jhyland87/Cryocooler-Controller/hardware/kicad/cryocooler.kicad_sch

## KiCad design hardware/kicad/cryocooler.kicad_sch (2026-10-04)

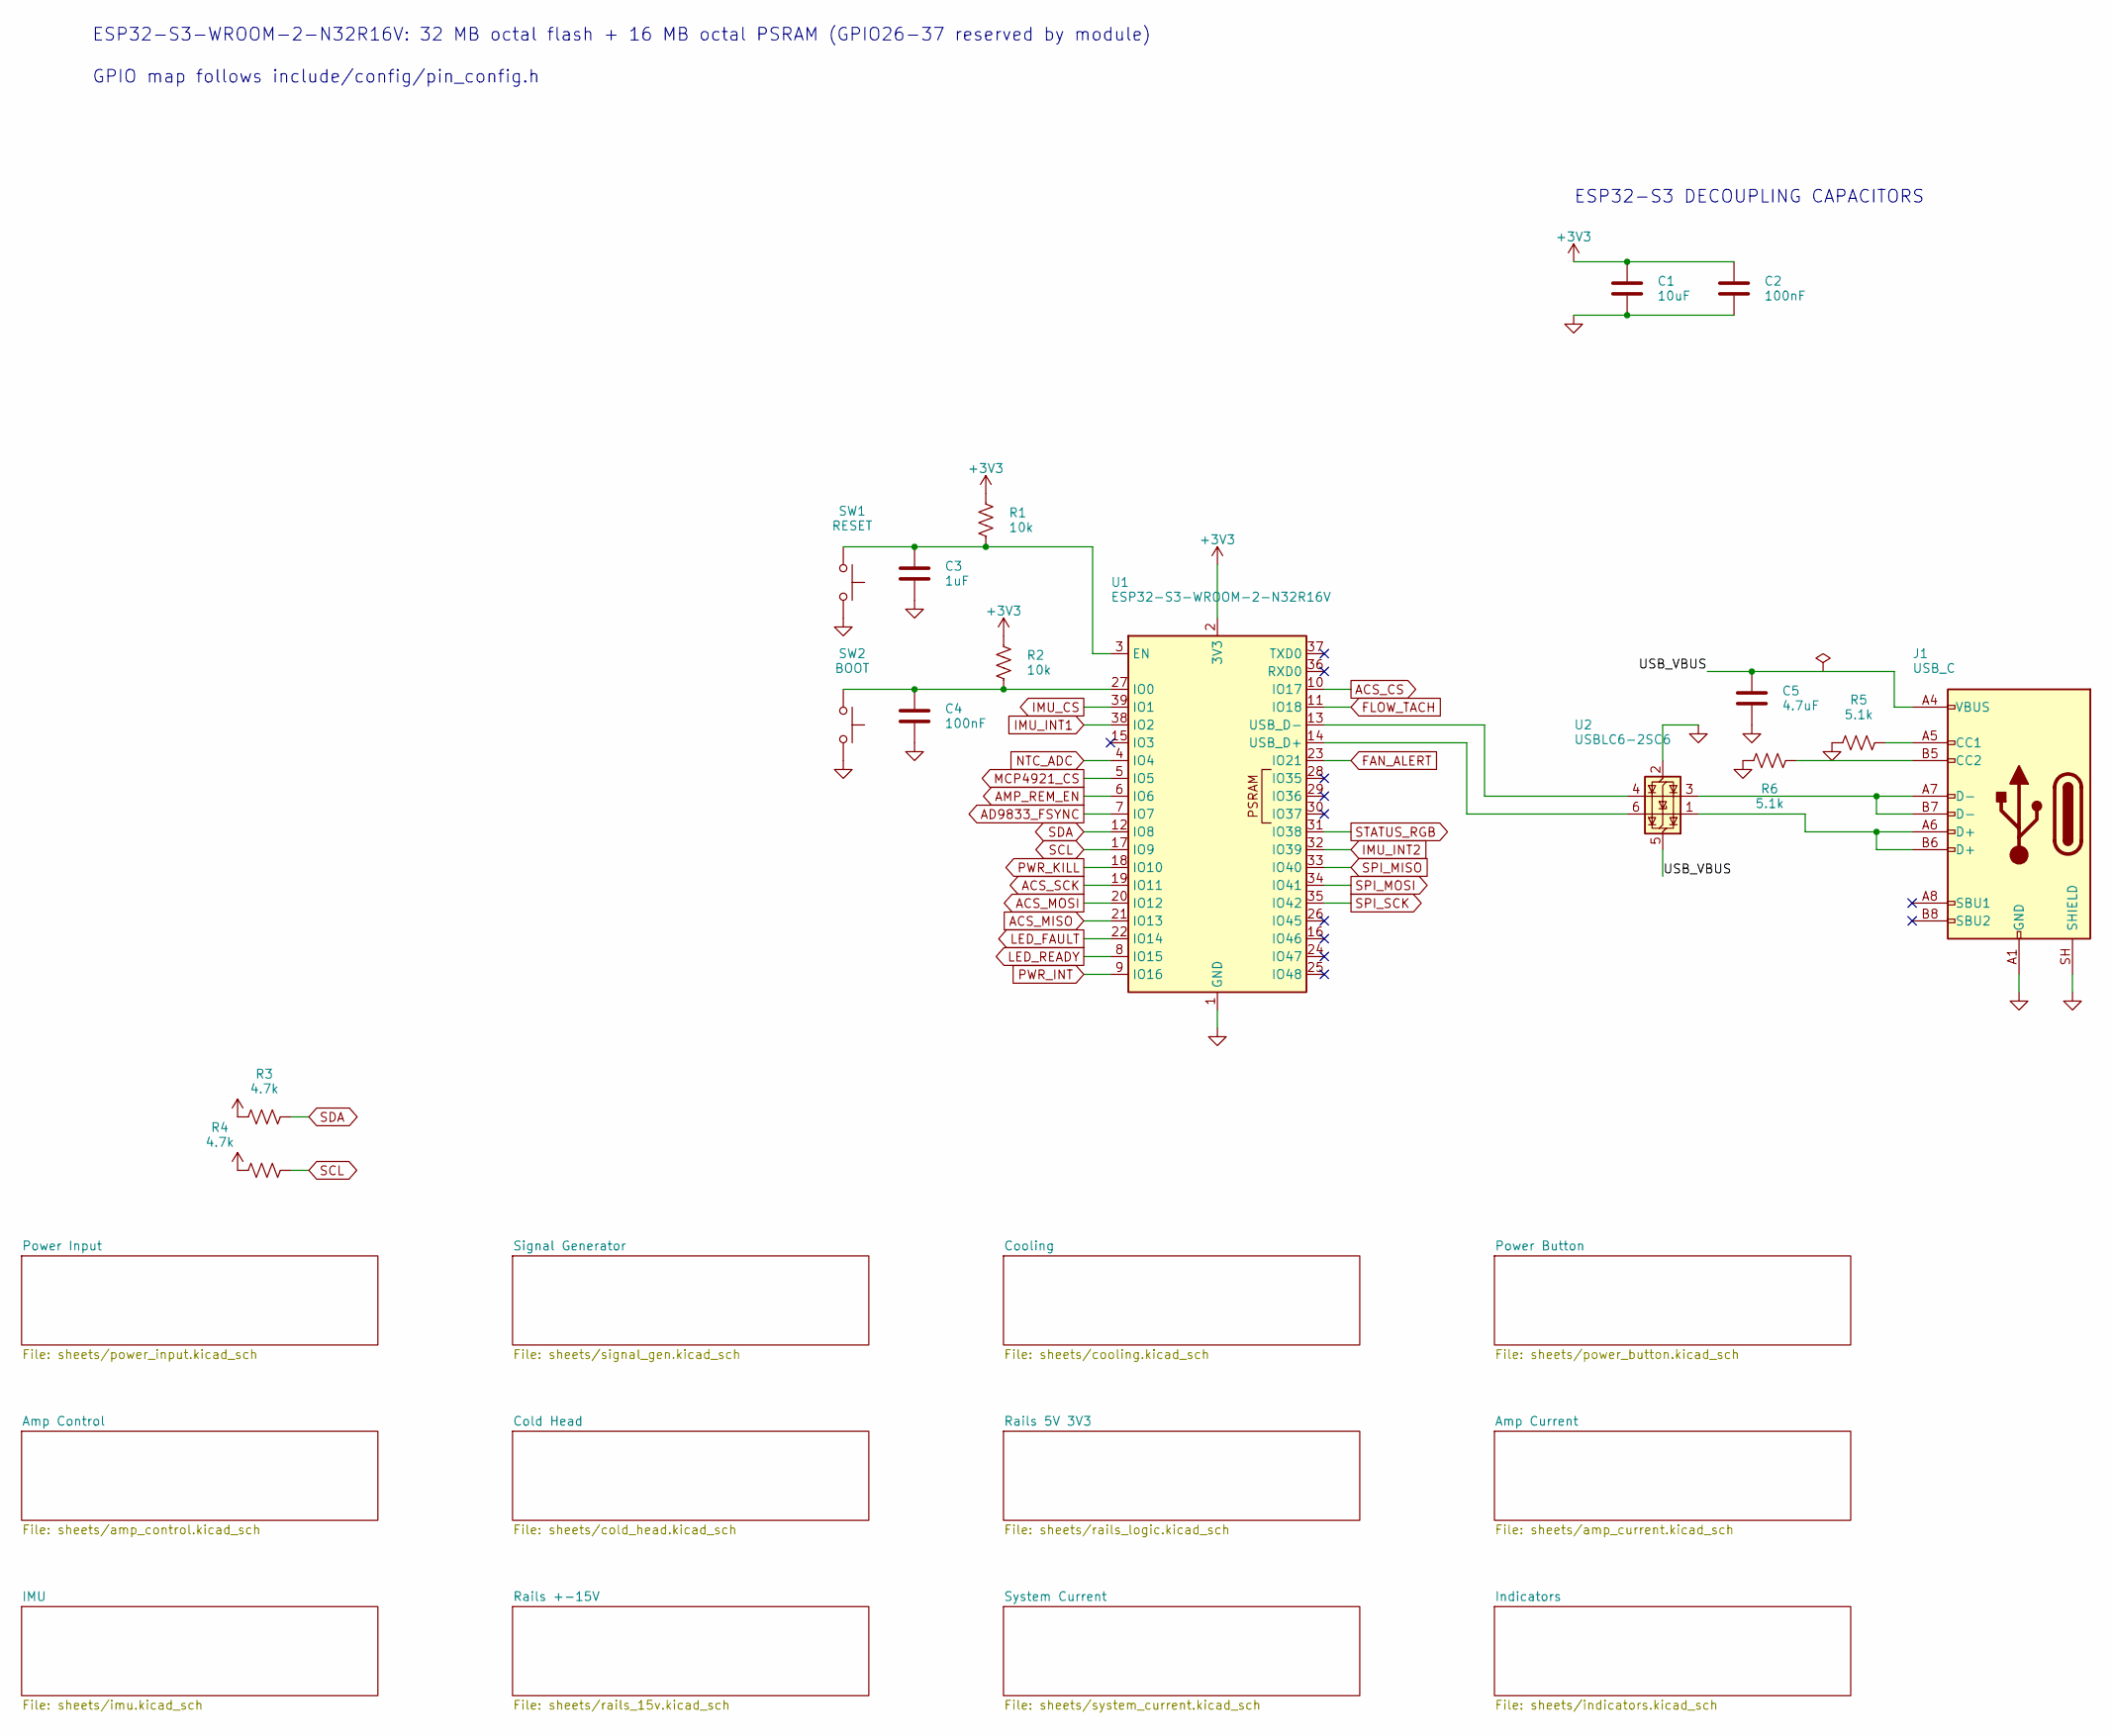
[picture p22: schematic cryocooler.kicad_sch]

Parts:
C1: 10uF; C_0805_2012Metric
C2, C4: 100nF; C_0603_1608Metric
C3: 1uF; C_0805_2012Metric
C5: 4.7uF; C_0805_2012Metric
J1: USB_C; USB_C_Receptacle_GCT_USB4105-xx-A_16P_TopMnt_Horizontal
R1, R2: 10k; R_0603_1608Metric
R3, R4: 4.7k; R_0603_1608Metric
R5, R6: 5.1k; R_0603_1608Metric
SW1: RESET; SW_SPST_TL3342
SW2: BOOT; SW_SPST_TL3342
U1: ESP32-S3-WROOM-2-N32R16V; ESP32-S3-WROOM-2
U2: USBLC6-2SC6; SOT-23-6

Connections:
+3V3: C1.1, C2.1, R1.1, R2.1, R3.1, R4.1, U1.2 (3V3)
ACS_CS: U1.10 (IO17)
ACS_MISO: U1.21 (IO13)
ACS_MOSI: U1.20 (IO12)
ACS_SCK: U1.19 (IO11)
AD9833_FSYNC: U1.7 (IO7)
AMP_REM_EN: U1.6 (IO6)
FAN_ALERT: U1.23 (IO21)
FLOW_TACH: U1.11 (IO18)
GND: C1.2, C2.2, C3.2, C4.2, C5.2, J1.A1 (GND), J1.A12 (GND), J1.B1 (GND), J1.B12 (GND), J1.SH (SHIELD), R5.1, R6.1, SW1.2, SW2.2, U1.1 (GND), U1.40 (GND), U1.41 (GND), U2.2 (GND)
IMU_CS: U1.39 (IO1)
IMU_INT1: U1.38 (IO2)
IMU_INT2: U1.32 (IO39)
LED_FAULT: U1.22 (IO14)
LED_READY: U1.8 (IO15)
MCP4921_CS: U1.5 (IO5)
NTC_ADC: U1.4 (IO4)
unnamed: C3.1, R1.2, SW1.1, U1.3 (EN)
unnamed: C4.1, R2.2, SW2.1, U1.27 (IO0)
unnamed: J1.A5 (CC1), R5.2
unnamed: J1.A6 (D+), J1.B6 (D+), U2.1 (I/O1)
unnamed: J1.A7 (D-), J1.B7 (D-), U2.3 (I/O2)
unnamed: J1.B5 (CC2), R6.2
unnamed: U1.13 (USB_D-), U2.4 (I/O2)
unnamed: U1.14 (USB_D+), U2.6 (I/O1)
PWR_INT: U1.9 (IO16)
PWR_KILL: U1.18 (IO10)
SCL: R4.2, U1.17 (IO9)
SDA: R3.2, U1.12 (IO8)
SPI_MISO: U1.33 (IO40)
SPI_MOSI: U1.34 (IO41)
SPI_SCK: U1.35 (IO42)
STATUS_RGB: U1.31 (IO38)
USB_VBUS: C5.1, J1.A4 (VBUS), J1.A9 (VBUS), J1.B4 (VBUS), J1.B9 (VBUS), U2.5 (VBUS)

Notes on the sheet:
GPIO map follows include/config/pin_config.h
ESP32-S3-WROOM-2-N32R16V: 32 MB octal flash + 16 MB octal PSRAM (GPIO26-37 reserved by module)
ESP32-S3 DECOUPLING CAPACITORS
