jhyland87/Cryocooler-Controller/hardware/kicad/sheets/amp_control.kicad_sch

## KiCad design hardware/kicad/sheets/amp_control.kicad_sch (2026-10-04)

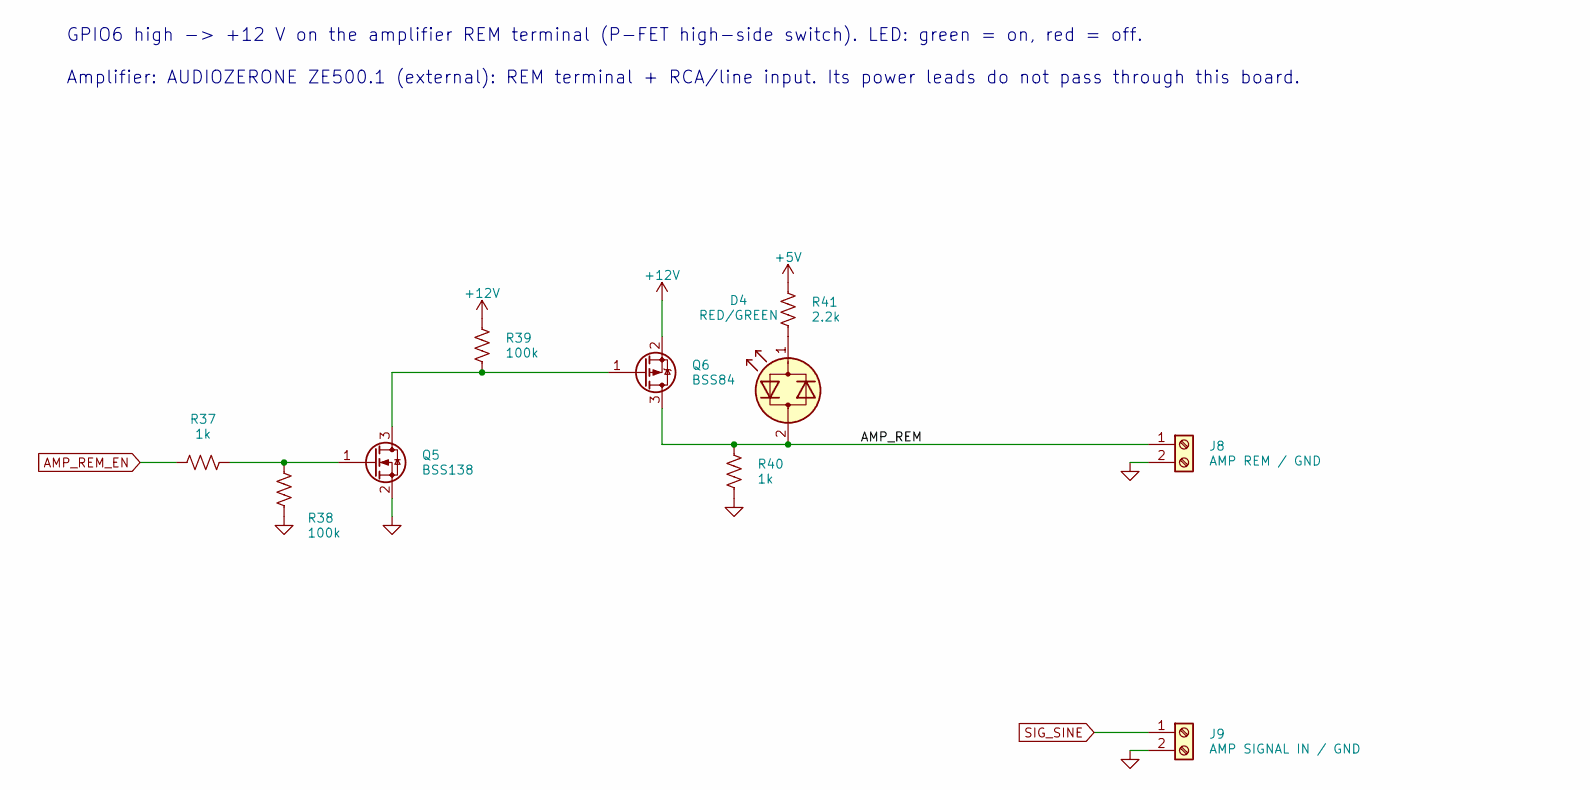
[picture p23: schematic amp_control.kicad_sch]

Parts:
D4: RED/GREEN; LED_1206_3216Metric
J8: AMP REM / GND; TerminalBlock_Phoenix_MKDS-1,5-2-5.08_1x02_P5.08mm_Horizont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
J9: AMP SIGNAL IN / GND; TerminalBlock_Phoenix_MKDS-1,5-2-5.08_1x02_P5.08mm_Horizont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
Q5: BSS138; SOT-23
Q6: BSS84; SOT-23
R37, R40: 1k; R_0603_1608Metric
R38, R39: 100k; R_0603_1608Metric
R41: 2.2k; R_0603_1608Metric

Connections:
+5V: R41.1
+12V: Q6.2 (S), R39.1
AMP_REM: D4.2 (AK), J8.1, Q6.3 (D), R40.1
AMP_REM_EN: R37.1
GND: J8.2, J9.2, Q5.2 (S), R38.2, R40.2
unnamed: D4.1 (KA), R41.2
unnamed: Q5.1 (G), R37.2, R38.1
unnamed: Q5.3 (D), Q6.1 (G), R39.2
SIG_SINE: J9.1

Notes on the sheet:
Amplifier: AUDIOZERONE ZE500.1 (external): REM terminal + RCA/line input. Its power leads do not pass through this board.
GPIO6 high -> +12 V on the amplifier REM terminal (P-FET high-side switch). LED: green = on, red = off.
