jhyland87/Cryocooler-Controller/hardware/kicad/sheets/amp_current.kicad_sch

## KiCad design hardware/kicad/sheets/amp_current.kicad_sch (2026-10-04)

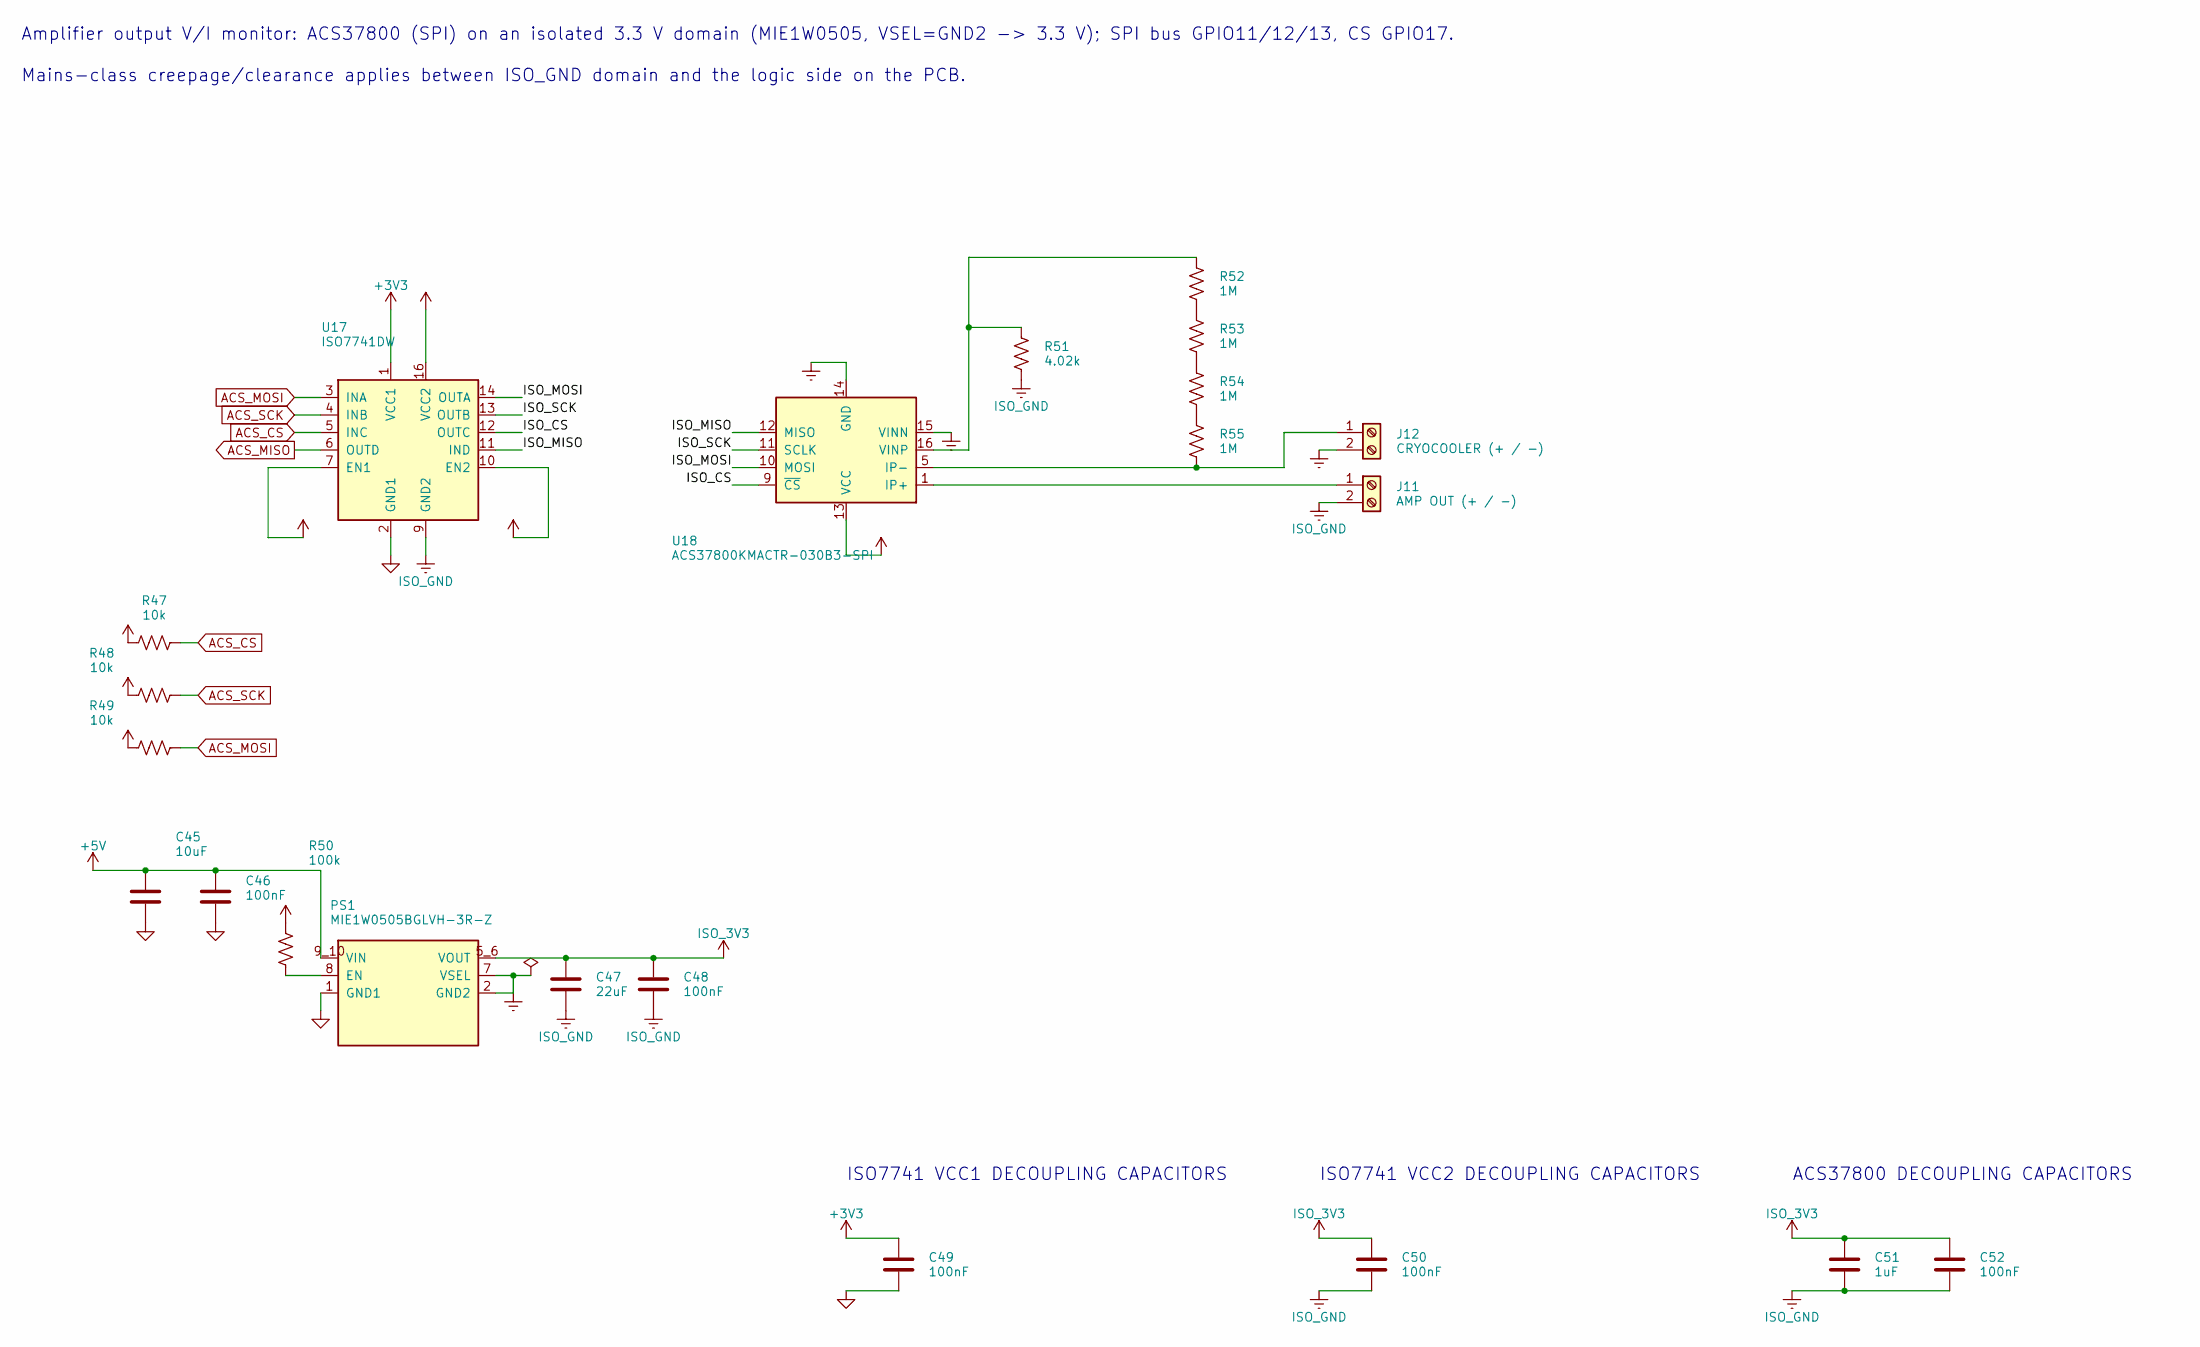
[picture p24: schematic amp_current.kicad_sch]

Parts:
C45: 10uF; C_0805_2012Metric
C46, C48, C49, C50, C52: 100nF; C_0603_1608Metric
C47: 22uF; C_1206_3216Metric
C51: 1uF; C_0805_2012Metric
J11: AMP OUT (+ / -); TerminalBlock_Phoenix_MKDS-1,5-2-5.08_1x02_P5.08mm_Horizont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
J12: CRYOCOOLER (+ / -); TerminalBlock_Phoenix_MKDS-1,5-2-5.08_1x02_P5.08mm_Horizont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
PS1: MIE1W0505BGLVH-3R-Z; CONV_MIE1W0505BGLVH-3R-Z
R47, R48, R49: 10k; R_0603_1608Metric
R50: 100k; R_0603_1608Metric
R51: 4.02k; R_0603_1608Metric
R52, R53, R54, R55: 1M; R_1206_3216Metric
U17: ISO7741DW; SOIC-16W_7.5x10.3mm_P1.27mm
U18: ACS37800KMACTR-030B3-SPI; SOIC-16W_7.5x10.3mm_P1.27mm

Connections:
+3V3: C49.1, R47.1, R48.1, R49.1, U17.1 (VCC1), U17.7 (EN1)
+5V: C45.1, C46.1, PS1.9_10 (VIN), R50.1
ACS_CS: R47.2, U17.5 (INC)
ACS_MISO: U17.6 (OUTD)
ACS_MOSI: R49.2, U17.3 (INA)
ACS_SCK: R48.2, U17.4 (INB)
GND: C45.2, C46.2, C49.2, PS1.1 (GND1), PS1.11_12 (GND1), U17.2 (GND1), U17.8 (GND1)
ISO_3V3: C47.1, C48.1, C50.1, C51.1, C52.1, PS1.5_6 (VOUT), U17.10 (EN2), U17.16 (VCC2), U18.13 (VCC)
ISO_CS: U17.12 (OUTC), U18.9 (~CS)
ISO_GND: C47.2, C48.2, C50.2, C51.2, C52.2, J11.2, J12.2, PS1.2 (GND2), PS1.3_4 (GND2), PS1.7 (VSEL), R51.2, U17.9 (GND2), U17.15 (GND2), U18.14 (GND), U18.15 (VINN)
ISO_MISO: U17.11 (IND), U18.12 (MISO)
ISO_MOSI: U17.14 (OUTA), U18.10 (MOSI)
ISO_SCK: U17.13 (OUTB), U18.11 (SCLK)
unnamed: J11.1, U18.1 (IP+), U18.2 (IP+), U18.3 (IP+), U18.4 (IP+)
unnamed: J12.1, R55.2, U18.5 (IP-), U18.6 (IP-), U18.7 (IP-), U18.8 (IP-)
unnamed: PS1.8 (EN), R50.2
unnamed: R51.1, R52.1, U18.16 (VINP)
unnamed: R52.2, R53.1
unnamed: R53.2, R54.1
unnamed: R54.2, R55.1

Notes on the sheet:
ACS37800 DECOUPLING CAPACITORS
ISO7741 VCC1 DECOUPLING CAPACITORS
Amplifier output V/I monitor: ACS37800 (SPI) on an isolated 3.3 V domain (MIE1W0505, VSEL=GND2 -> 3.3 V); SPI bus GPIO11/12/13, CS GPIO17.
ISO7741 VCC2 DECOUPLING CAPACITORS
Mains-class creepage/clearance applies between ISO_GND domain and the logic side on the PCB.
