jhyland87/Cryocooler-Controller/hardware/kicad/sheets/cold_head.kicad_sch

## KiCad design hardware/kicad/sheets/cold_head.kicad_sch (2026-10-04)

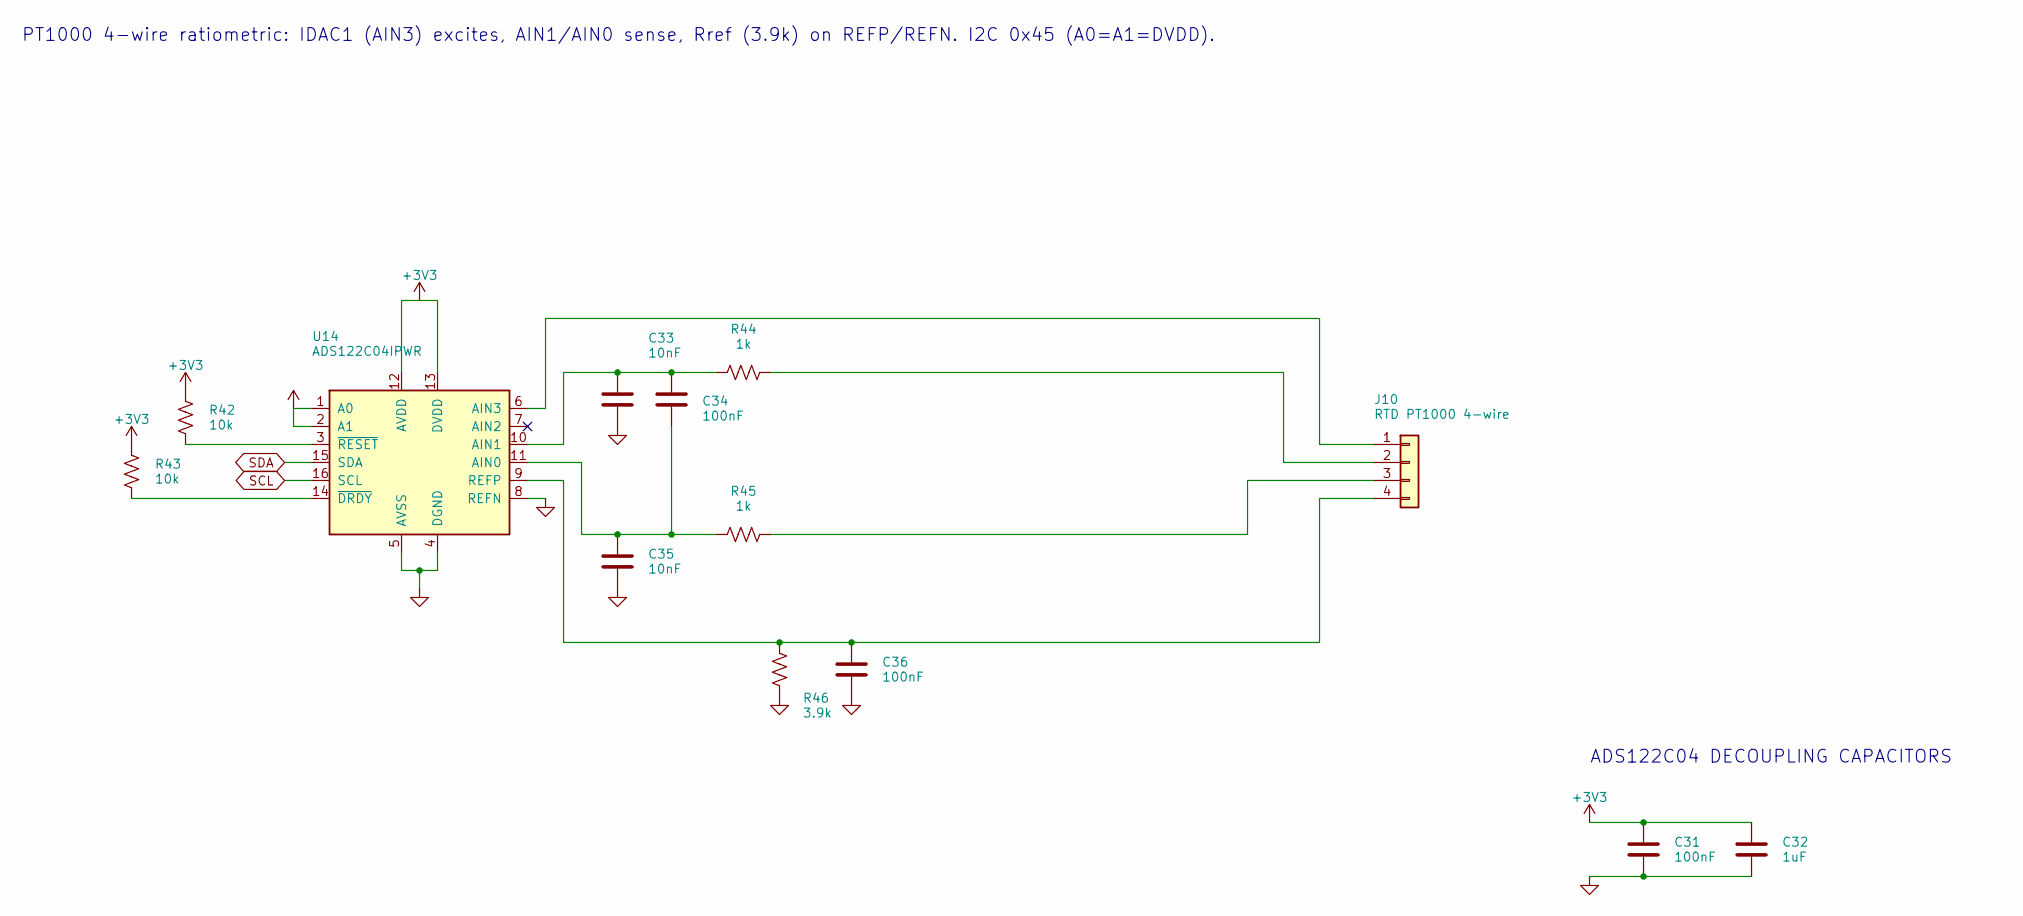
[picture p25: schematic cold_head.kicad_sch]

Parts:
C31, C34, C36: 100nF; C_0603_1608Metric
C32: 1uF; C_0805_2012Metric
C33, C35: 10nF; C_0603_1608Metric
J10: RTD PT1000 4-wire; JST_XH_B4B-XH-A_1x04_P2.50mm_Vertical
R42, R43: 10k; R_0603_1608Metric
R44, R45: 1k; R_0603_1608Metric
R46: 3.9k; R_0603_1608Metric
U14: ADS122C04IPWR; TSSOP-16_4.4x5mm_P0.65mm

Connections:
+3V3: C31.1, C32.1, R42.1, R43.1, U14.1 (A0), U14.2 (A1), U14.12 (AVDD), U14.13 (DVDD)
GND: C31.2, C32.2, C33.2, C35.2, C36.2, R46.2, U14.4 (DGND), U14.5 (AVSS), U14.8 (REFN)
unnamed: C33.1, C34.1, R44.1, U14.10 (AIN1)
unnamed: C34.2, C35.1, R45.1, U14.11 (AIN0)
unnamed: C36.1, J10.4, R46.1, U14.9 (REFP)
unnamed: J10.1, U14.6 (AIN3)
unnamed: J10.2, R44.2
unnamed: J10.3, R45.2
unnamed: R42.2, U14.3 (~RESET)
unnamed: R43.2, U14.14 (~DRDY)
SCL: U14.16 (SCL)
SDA: U14.15 (SDA)

Notes on the sheet:
ADS122C04 DECOUPLING CAPACITORS
PT1000 4-wire ratiometric: IDAC1 (AIN3) excites, AIN1/AIN0 sense, Rref (3.9k) on REFP/REFN. I2C 0x45 (A0=A1=DVDD).
