jhyland87/Cryocooler-Controller/hardware/kicad/sheets/cooling.kicad_sch

## KiCad design hardware/kicad/sheets/cooling.kicad_sch (2026-10-04)

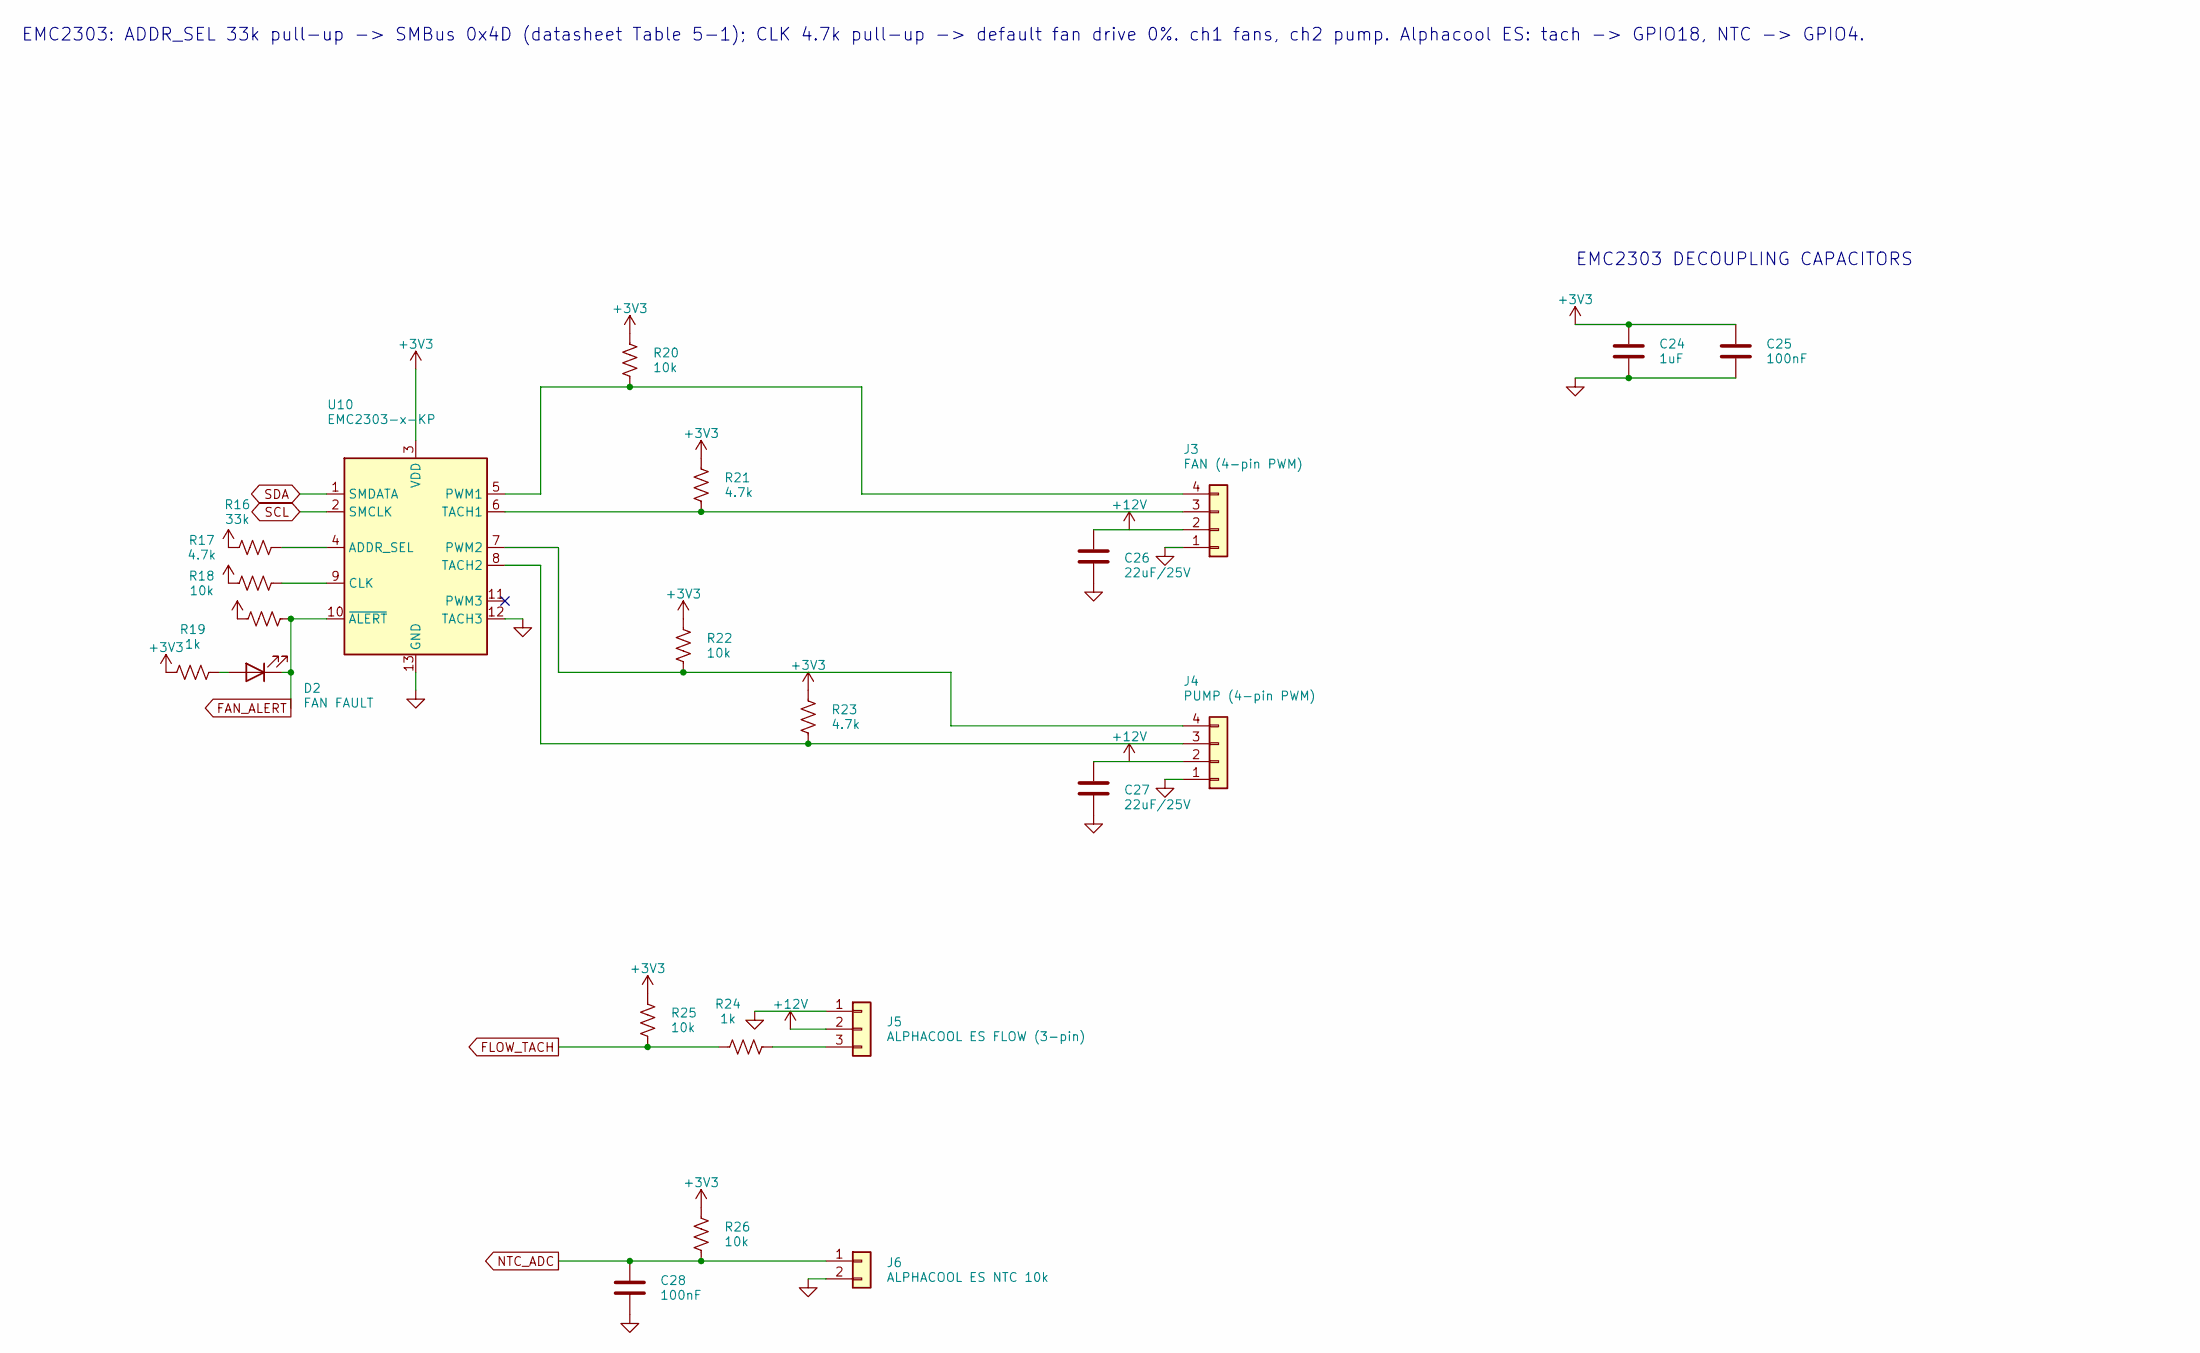
[picture p26: schematic cooling.kicad_sch]

Parts:
C24: 1uF; C_0805_2012Metric
C25, C28: 100nF; C_0603_1608Metric
C26, C27: 22uF/25V; C_1210_3225Metric
D2: FAN FAULT; LED_0603_1608Metric
J3: FAN (4-pin PWM); Molex_KK-254_AE-6410-04A_1x04_P2.54mm_Vertical
J4: PUMP (4-pin PWM); Molex_KK-254_AE-6410-04A_1x04_P2.54mm_Vertical
J5: ALPHACOOL ES FLOW (3-pin); Molex_KK-254_AE-6410-03A_1x03_P2.54mm_Vertical
J6: ALPHACOOL ES NTC 10k; JST_XH_B2B-XH-A_1x02_P2.50mm_Vertical
R16: 33k; R_0603_1608Metric
R17, R21, R23: 4.7k; R_0603_1608Metric
R18, R20, R22, R25, R26: 10k; R_0603_1608Metric
R19, R24: 1k; R_0603_1608Metric
U10: EMC2303-x-KP; VQFN-12-1EP_4x4mm_P0.8mm_EP2.1x2.1mm_ThermalVias

Connections:
+3V3: C24.1, C25.1, R16.1, R17.1, R18.1, R19.1, R20.1, R21.1, R22.1, R23.1, R25.1, R26.1, U10.3 (VDD)
+12V: C26.1, C27.1, J3.2, J4.2, J5.2
FAN_ALERT: D2.1 (K), R18.2, U10.10 (~ALERT)
FLOW_TACH: R24.1, R25.2
GND: C24.2, C25.2, C26.2, C27.2, C28.2, J3.1, J4.1, J5.1, J6.2, U10.12 (TACH3), U10.13 (GND)
NTC_ADC: C28.1, J6.1, R26.2
unnamed: D2.2 (A), R19.2
unnamed: J3.3, R21.2, U10.6 (TACH1)
unnamed: J3.4, R20.2, U10.5 (PWM1)
unnamed: J4.3, R23.2, U10.8 (TACH2)
unnamed: J4.4, R22.2, U10.7 (PWM2)
unnamed: J5.3, R24.2
unnamed: R16.2, U10.4 (ADDR_SEL)
unnamed: R17.2, U10.9 (CLK)
SCL: U10.2 (SMCLK)
SDA: U10.1 (SMDATA)

Notes on the sheet:
EMC2303: ADDR_SEL 33k pull-up -> SMBus 0x4D (datasheet Table 5-1); CLK 4.7k pull-up -> default fan drive 0%. ch1 fans, ch2 pump. Alphacool ES: tach -> GPIO18, NTC -> GPIO4.
EMC2303 DECOUPLING CAPACITORS
