jhyland87/Cryocooler-Controller/hardware/kicad/sheets/imu.kicad_sch

## KiCad design hardware/kicad/sheets/imu.kicad_sch (2026-10-04)

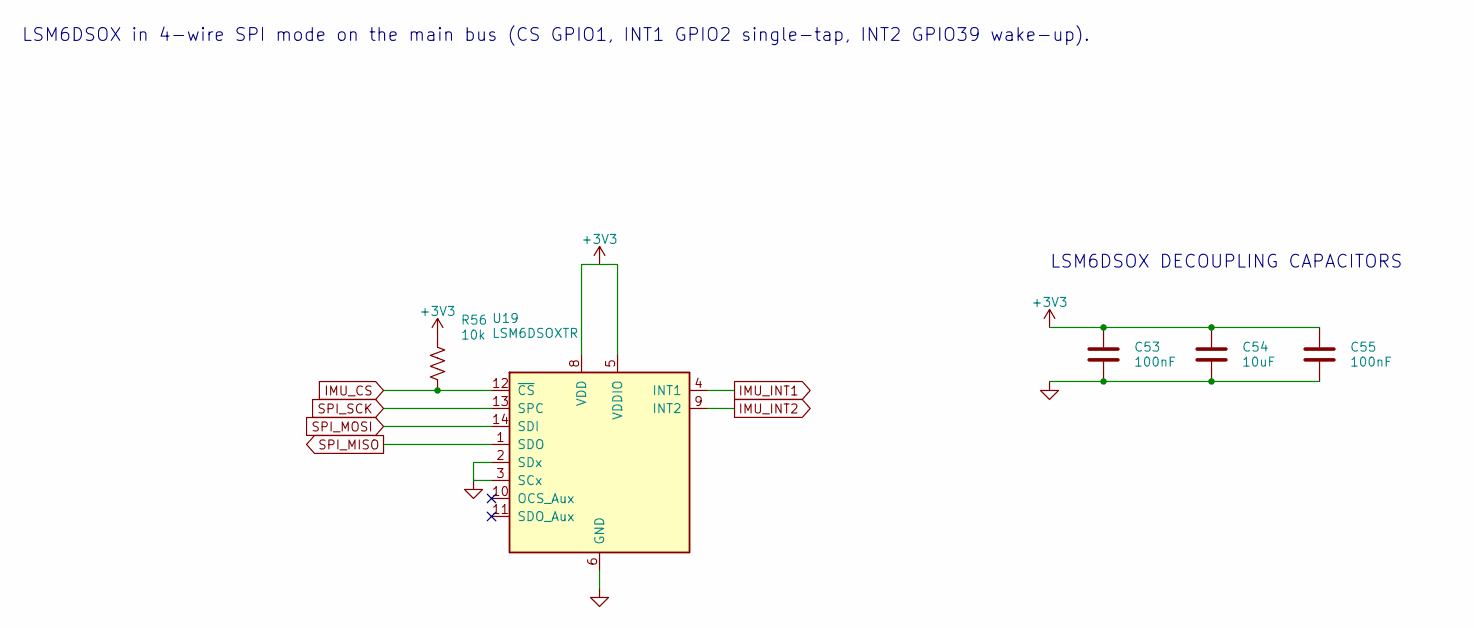
[picture p27: schematic imu.kicad_sch]

Parts:
C53, C55: 100nF; C_0603_1608Metric
C54: 10uF; C_0805_2012Metric
R56: 10k; R_0603_1608Metric
U19: LSM6DSOXTR; LGA-14_3x2.5mm_P0.5mm_LayoutBorder3x4y

Connections:
+3V3: C53.1, C54.1, C55.1, R56.1, U19.5 (VDDIO), U19.8 (VDD)
GND: C53.2, C54.2, C55.2, U19.2 (SDx), U19.3 (SCx), U19.6 (GND), U19.7 (GND)
IMU_CS: R56.2, U19.12 (~CS)
IMU_INT1: U19.4 (INT1)
IMU_INT2: U19.9 (INT2)
SPI_MISO: U19.1 (SDO)
SPI_MOSI: U19.14 (SDI)
SPI_SCK: U19.13 (SPC)

Notes on the sheet:
LSM6DSOX in 4-wire SPI mode on the main bus (CS GPIO1, INT1 GPIO2 single-tap, INT2 GPIO39 wake-up).
LSM6DSOX DECOUPLING CAPACITORS
