jhyland87/Cryocooler-Controller/hardware/kicad/sheets/indicators.kicad_sch

## KiCad design hardware/kicad/sheets/indicators.kicad_sch (2026-10-04)

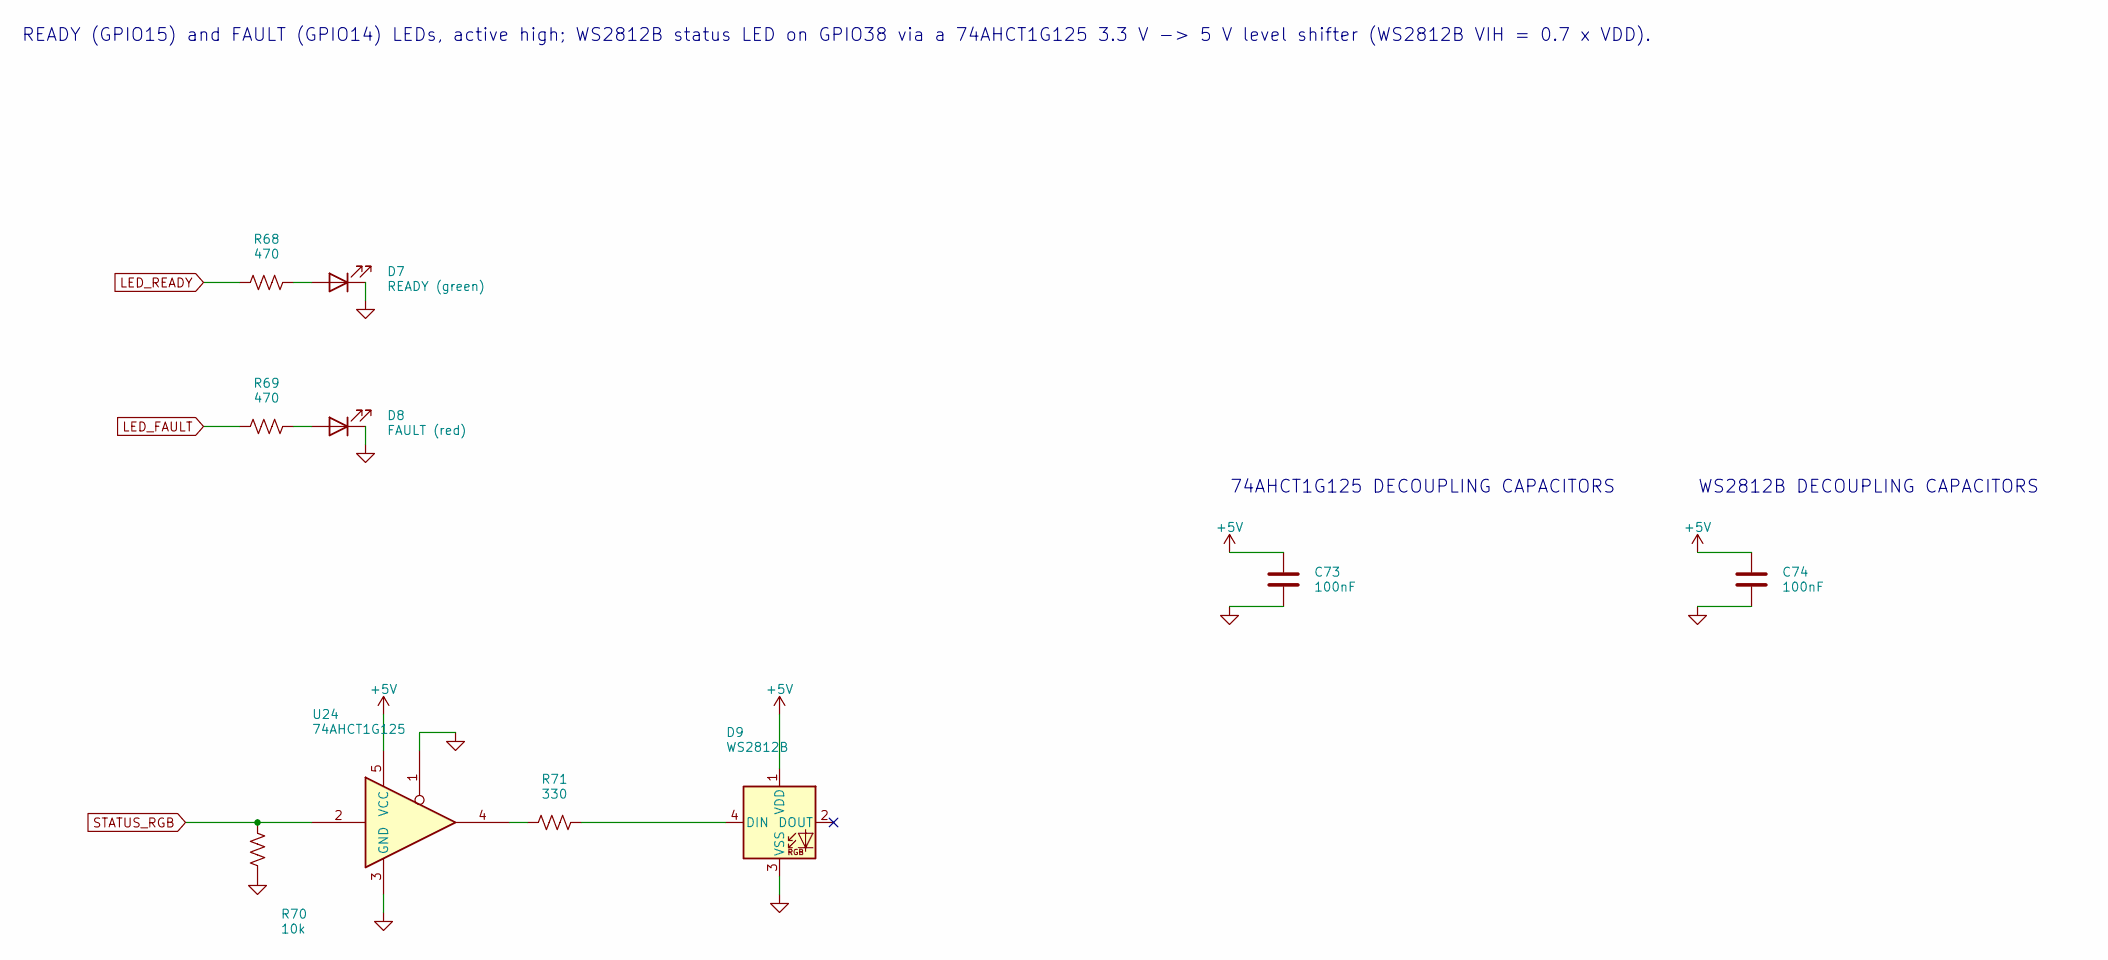
[picture p28: schematic indicators.kicad_sch]

Parts:
C73, C74: 100nF; C_0603_1608Metric
D7: READY (green); LED_0603_1608Metric
D8: FAULT (red); LED_0603_1608Metric
D9: WS2812B; LED_WS2812B_PLCC4_5.0x5.0mm_P3.2mm
R68, R69: 470; R_0603_1608Metric
R70: 10k; R_0603_1608Metric
R71: 330; R_0603_1608Metric
U24: 74AHCT1G125; SOT-23-5

Connections:
+5V: C73.1, C74.1, D9.1 (VDD), U24.5 (VCC)
GND: C73.2, C74.2, D7.1 (K), D8.1 (K), D9.3 (VSS), R70.2, U24.1, U24.3 (GND)
LED_FAULT: R69.1
LED_READY: R68.1
unnamed: D7.2 (A), R68.2
unnamed: D8.2 (A), R69.2
unnamed: D9.4 (DIN), R71.2
unnamed: R71.1, U24.4
STATUS_RGB: R70.1, U24.2

Notes on the sheet:
READY (GPIO15) and FAULT (GPIO14) LEDs, active high; WS2812B status LED on GPIO38 via a 74AHCT1G125 3.3 V -> 5 V level shifter (WS2812B VIH = 0.7 x VDD).
74AHCT1G125 DECOUPLING CAPACITORS
WS2812B DECOUPLING CAPACITORS
