jhyland87/Cryocooler-Controller/hardware/kicad/sheets/power_button.kicad_sch

## KiCad design hardware/kicad/sheets/power_button.kicad_sch (2026-10-04)

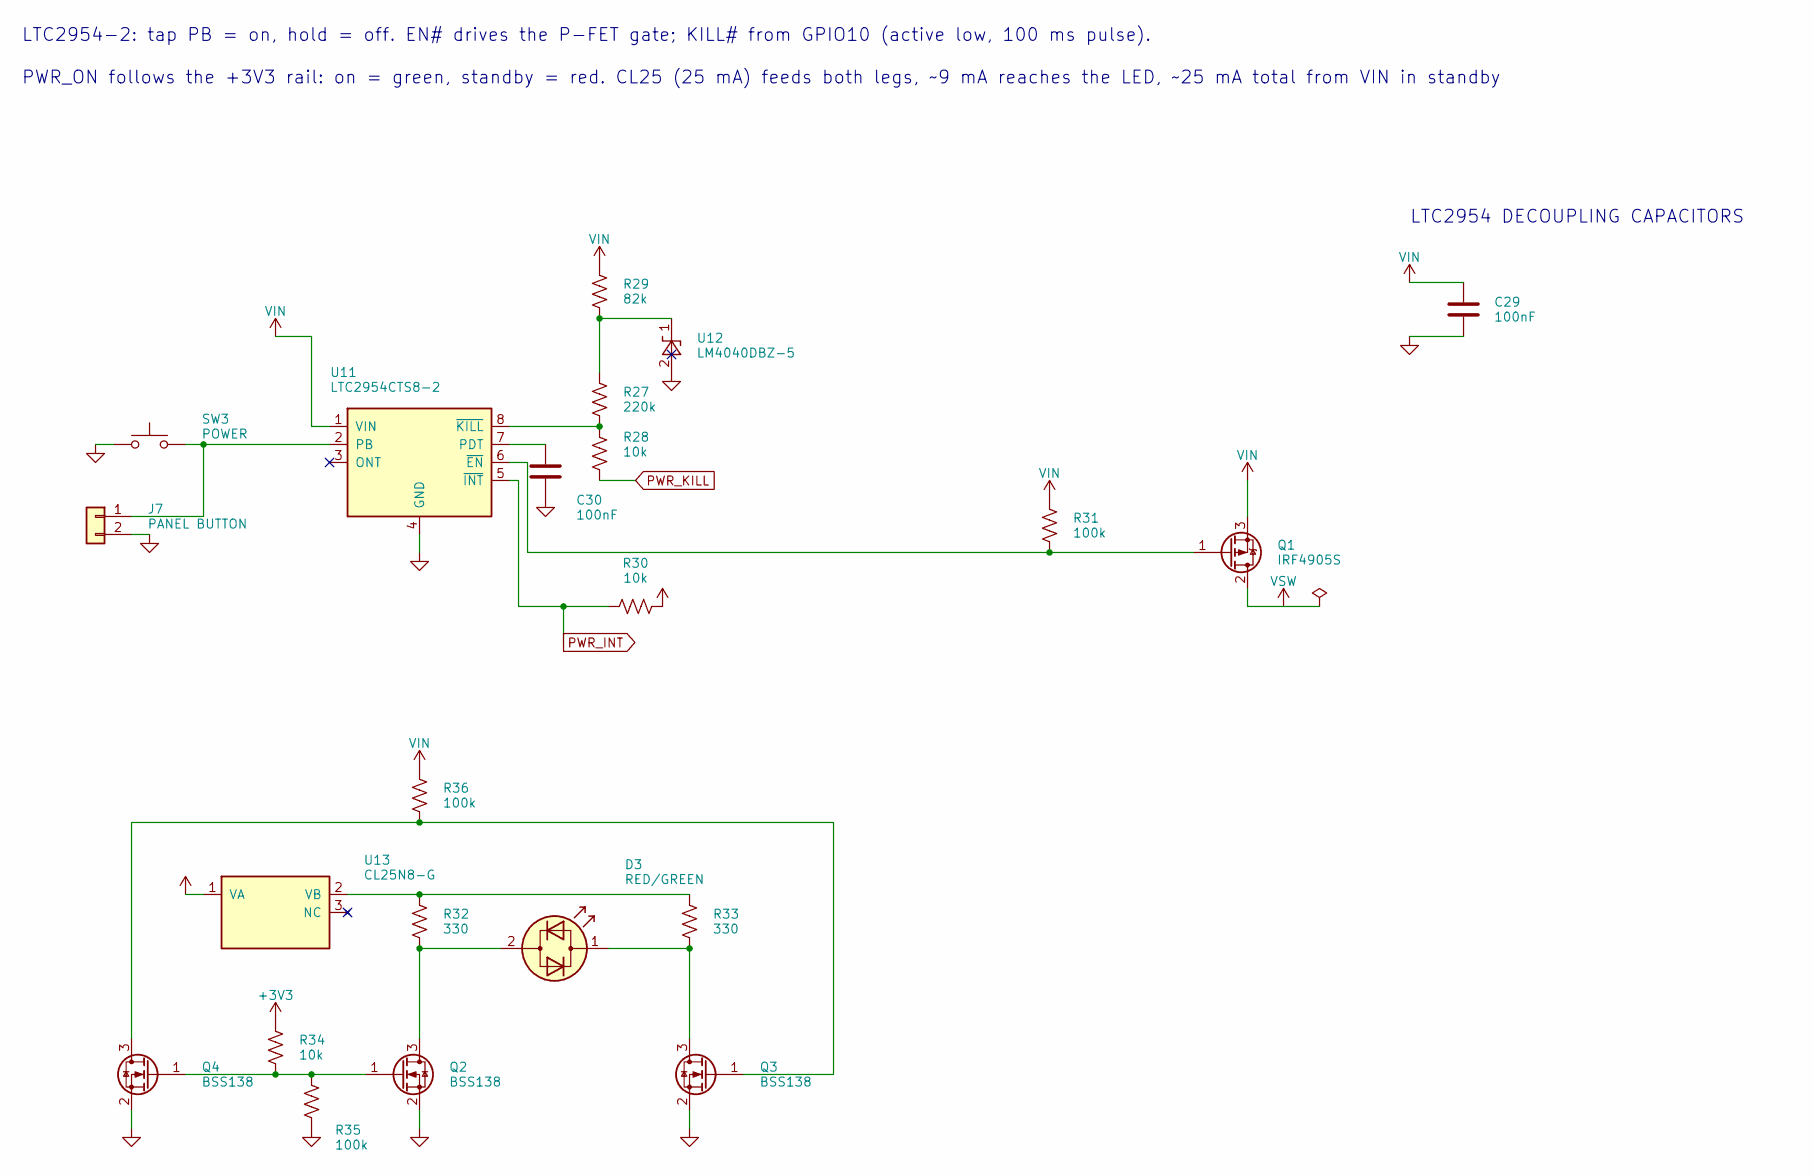
[picture p29: schematic power_button.kicad_sch]

Parts:
C29, C30: 100nF; C_0603_1608Metric
D3: RED/GREEN; LED_1206_3216Metric
J7: PANEL BUTTON; JST_XH_B2B-XH-A_1x02_P2.50mm_Vertical
Q1: IRF4905S; TO-263-3_TabPin2
Q2, Q3, Q4: BSS138; SOT-23
R27: 220k; R_0603_1608Metric
R28, R30, R34: 10k; R_0603_1608Metric
R29: 82k; R_0603_1608Metric
R31, R35, R36: 100k; R_0603_1608Metric
R32, R33: 330; R_0603_1608Metric
SW3: POWER; SW_SPST_TL3342
U11: LTC2954CTS8-2; SOT-23-8
U12: LM4040DBZ-5; SOT-23
U13: CL25N8-G; SOT-89-3

Connections:
+3V3: R30.2, R34.1
GND: C29.2, C30.2, J7.2, Q2.2 (S), Q3.2 (S), Q4.2 (S), R35.2, SW3.2, U11.4 (GND), U12.2 (A)
unnamed: C30.1, U11.7 (PDT)
unnamed: D3.1 (KA), Q3.3 (D), R33.2
unnamed: D3.2 (AK), Q2.3 (D), R32.2
unnamed: J7.1, SW3.1, U11.2 (PB)
unnamed: Q1.1 (G), R31.2, U11.6 (~EN)
unnamed: Q2.1 (G), Q4.1 (G), R34.2, R35.1
unnamed: Q3.1 (G), Q4.3 (D), R36.2
unnamed: R27.1, R29.2, U12.1 (K)
unnamed: R27.2, R28.1, U11.8 (~KILL)
unnamed: R32.1, R33.1, U13.2 (VB)
PWR_INT: R30.1, U11.5 (~INT)
PWR_KILL: R28.2
VIN: C29.1, Q1.3 (S), R29.1, R31.1, R36.1, U11.1 (VIN), U13.1 (VA)
VSW: Q1.2 (D)

Notes on the sheet:
PWR_ON follows the +3V3 rail: on = green, standby = red. CL25 (25 mA) feeds both legs, ~9 mA reaches the LED, ~25 mA total from VIN in standby
LTC2954 DECOUPLING CAPACITORS
LTC2954-2: tap PB = on, hold = off. EN# drives the P-FET gate; KILL# from GPIO10 (active low, 100 ms pulse).
