jhyland87/Cryocooler-Controller/hardware/kicad/sheets/power_input.kicad_sch

## KiCad design hardware/kicad/sheets/power_input.kicad_sch (2026-10-04)

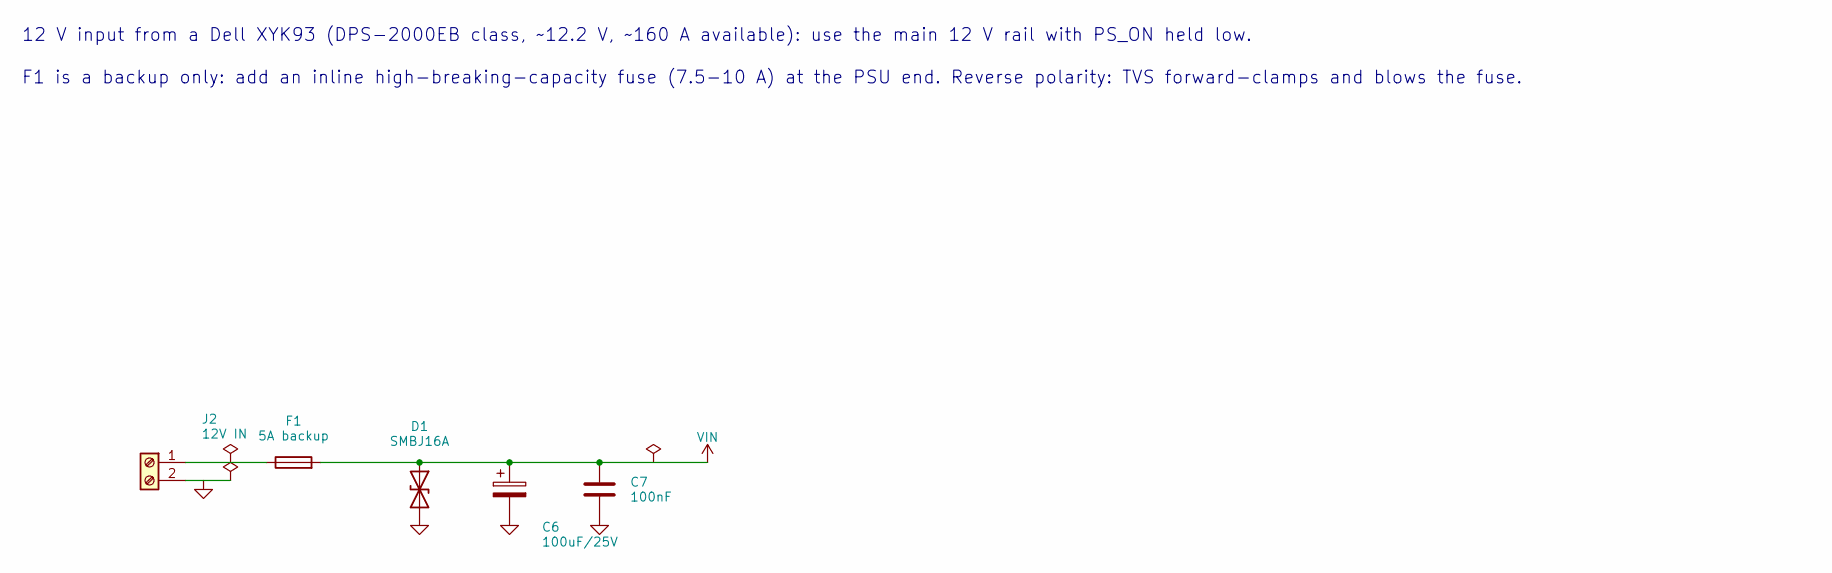
[picture p30: schematic power_input.kicad_sch]

Parts:
C6: 100uF/25V; CP_Elec_8x10
C7: 100nF; C_0805_2012Metric
D1: SMBJ16A; D_SMB
F1: 5A backup; Fuse_1812_4532Metric
J2: 12V IN; TerminalBlock_Phoenix_MKDS-1,5-2-5.08_1x02_P5.08mm_Horizont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

Connections:
GND: C6.2, C7.2, D1.2 (A2), J2.2
unnamed: F1.1, J2.1
VIN: C6.1, C7.1, D1.1 (A1), F1.2

Notes on the sheet:
12 V input from a Dell XYK93 (DPS-2000EB class, ~12.2 V, ~160 A available): use the main 12 V rail with PS_ON held low.
F1 is a backup only: add an inline high-breaking-capacity fuse (7.5-10 A) at the PSU end. Reverse polarity: TVS forward-clamps and blows the fuse.
