jhyland87/Cryocooler-Controller/hardware/kicad/sheets/rails_15v.kicad_sch

## KiCad design hardware/kicad/sheets/rails_15v.kicad_sch (2026-10-04)

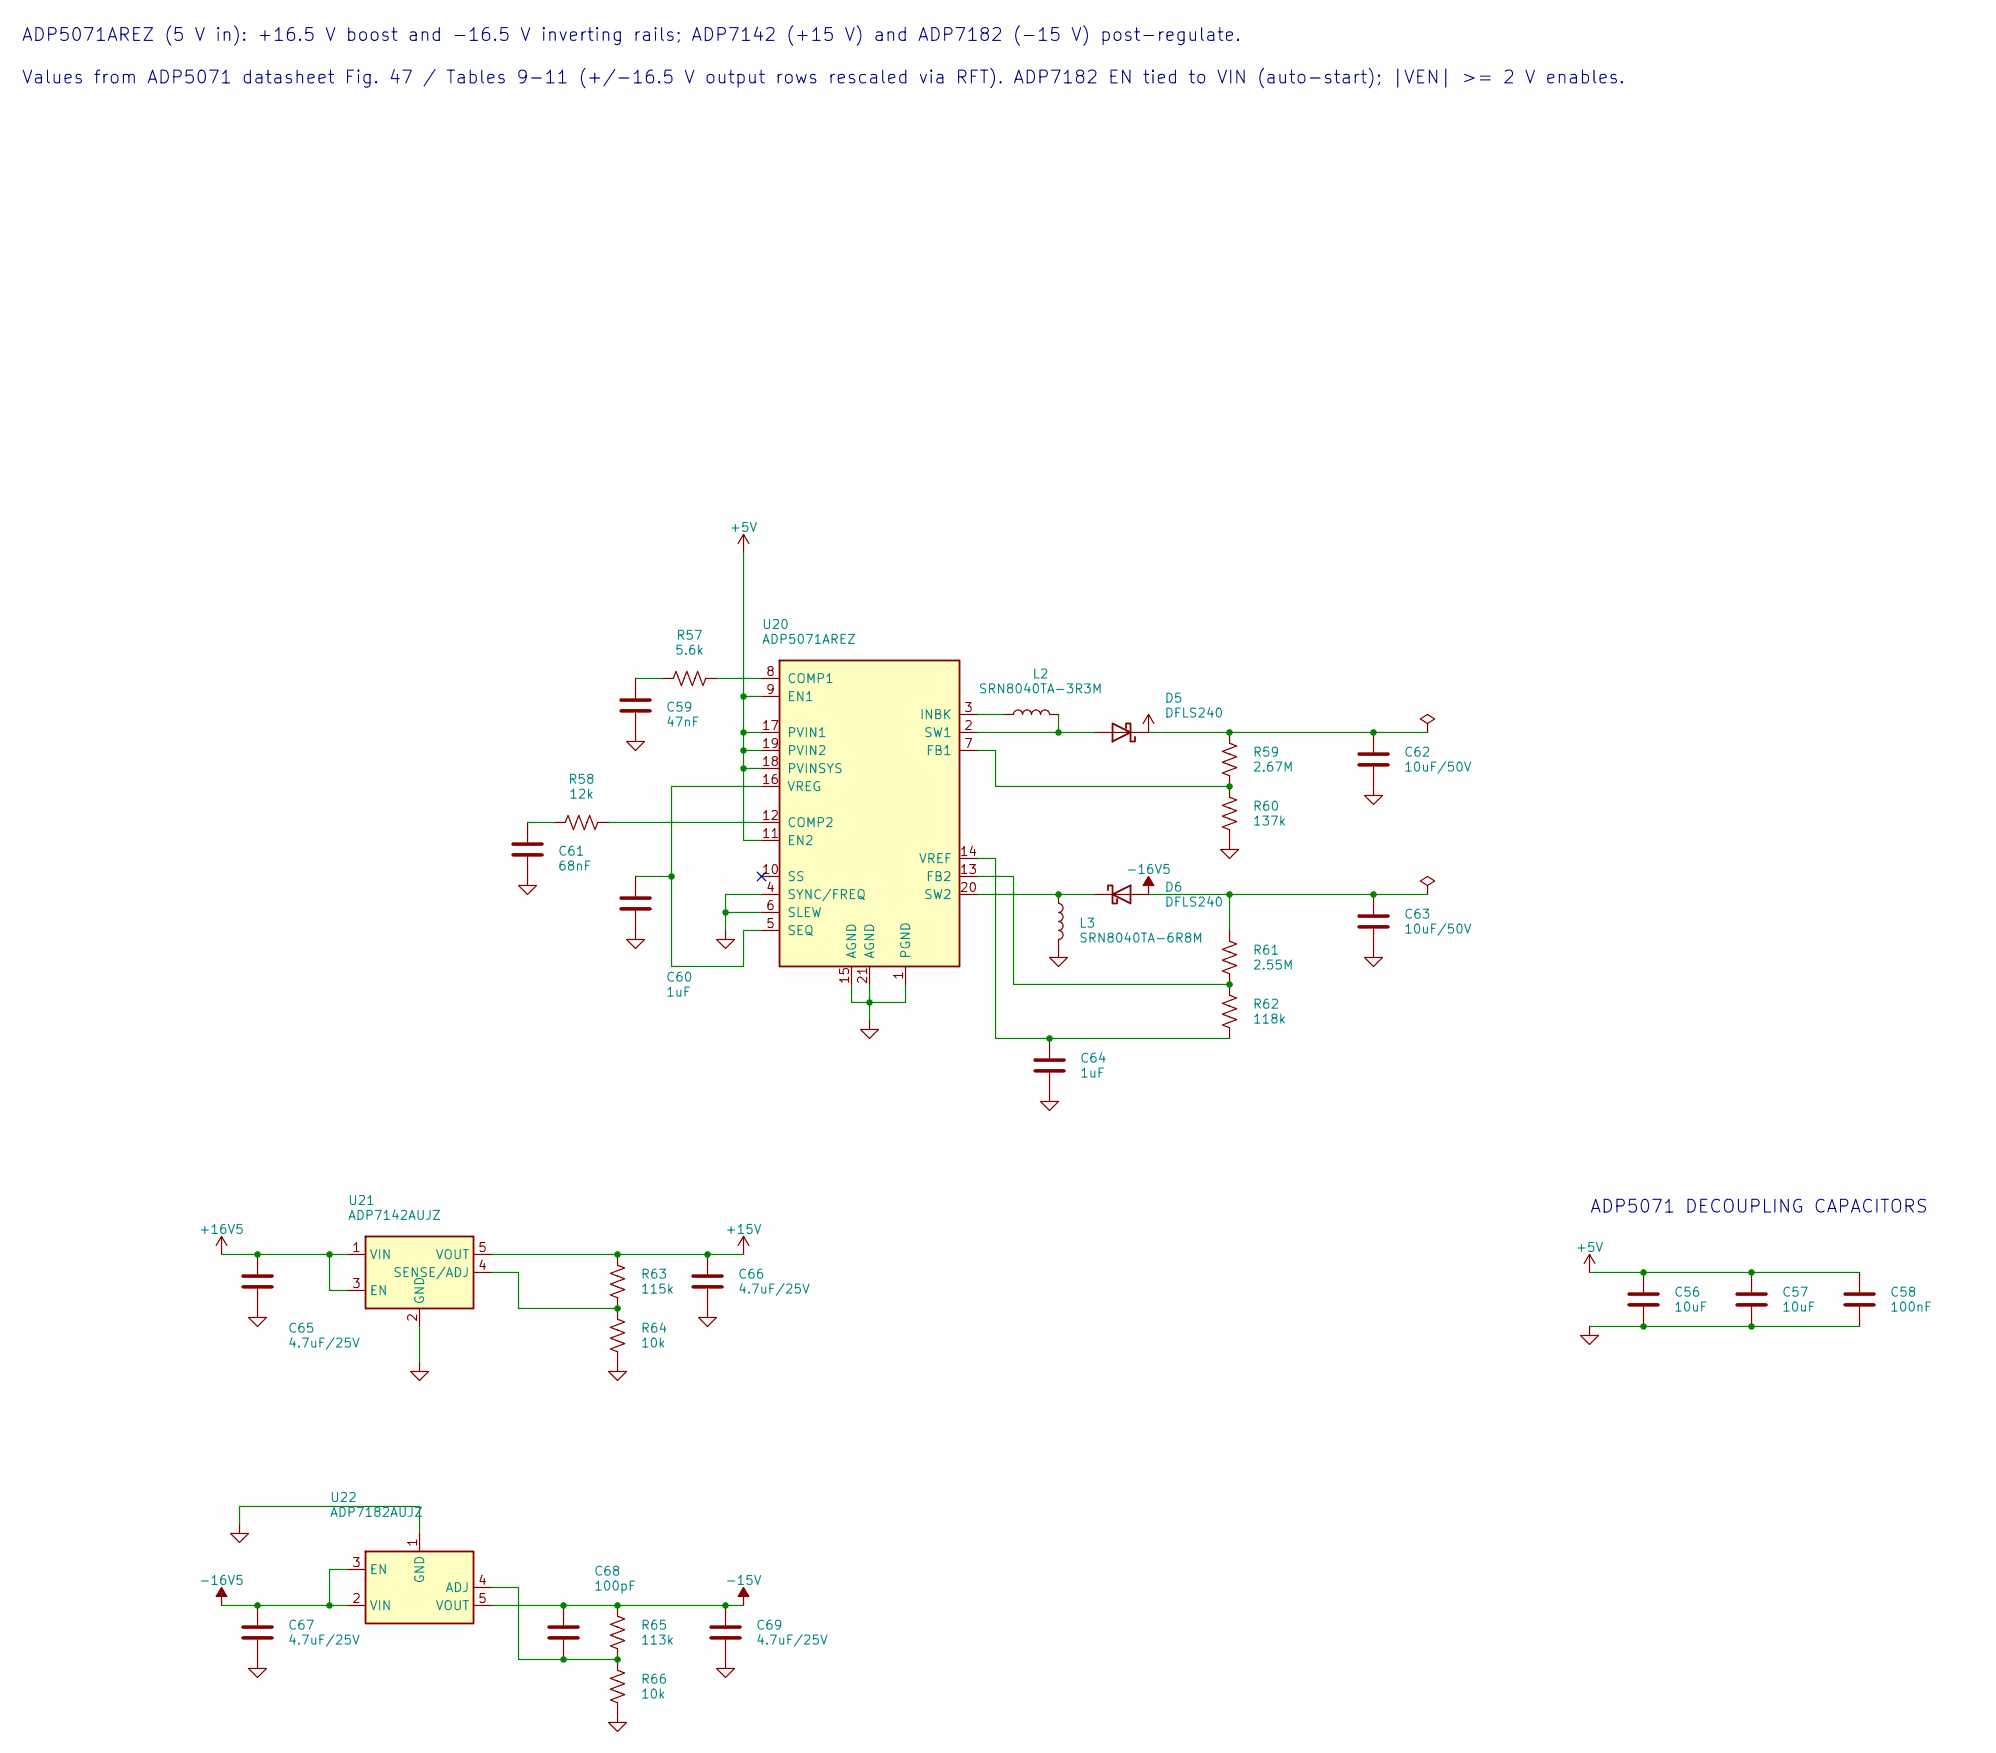
[picture p31: schematic rails_15v.kicad_sch]

Parts:
C56, C57: 10uF; C_0805_2012Metric
C58: 100nF; C_0603_1608Metric
C59: 47nF; C_1206_3216Metric
C60, C64: 1uF; C_0805_2012Metric
C61: 68nF; C_1206_3216Metric
C62, C63: 10uF/50V; C_1210_3225Metric
C65, C66, C67, C69: 4.7uF/25V; C_1206_3216Metric
C68: 100pF; C_1206_3216Metric
D5, D6: DFLS240; D_PowerDI-123
L2: SRN8040TA-3R3M; L_Bourns_SRN8040TA
L3: SRN8040TA-6R8M; L_Bourns_SRN8040TA
R57: 5.6k; R_0603_1608Metric
R58: 12k; R_0603_1608Metric
R59: 2.67M; R_0603_1608Metric
R60: 137k; R_0603_1608Metric
R61: 2.55M; R_0603_1608Metric
R62: 118k; R_0603_1608Metric
R63: 115k; R_0603_1608Metric
R64, R66: 10k; R_0603_1608Metric
R65: 113k; R_0603_1608Metric
U20: ADP5071AREZ; ETSSOP-20-1EP_4.4x6.5mm_P0.65mm_EP3x4.2mm
U21: ADP7142AUJZ; TSOT-23-5
U22: ADP7182AUJZ; TSOT-23-5

Connections:
+5V: C56.1, C57.1, C58.1, U20.9 (EN1), U20.11 (EN2), U20.17 (PVIN1), U20.18 (PVINSYS), U20.19 (PVIN2)
+15V: C66.1, R63.1, U21.5 (VOUT)
+16V5: C62.1, C65.1, D5.1 (K), R59.1, U21.1 (VIN), U21.3 (EN)
-15V: C68.1, C69.1, R65.1, U22.5 (VOUT)
-16V5: C63.1, C67.1, D6.2 (A), R61.1, U22.2 (VIN), U22.3 (EN)
GND: C56.2, C57.2, C58.2, C59.2, C60.2, C61.2, C62.2, C63.2, C64.2, C65.2, C66.2, C67.2, C69.2, L3.2, R60.2, R64.2, R66.2, U20.1 (PGND), U20.4 (SYNC/FREQ), U20.6 (SLEW), U20.15 (AGND), U20.21 (AGND), U21.2 (GND), U22.1 (GND)
unnamed: C59.1, R57.1
unnamed: C60.1, U20.5 (SEQ), U20.16 (VREG)
unnamed: C61.1, R58.1
unnamed: C64.1, R62.2, U20.14 (VREF)
unnamed: C68.2, R65.2, R66.1, U22.4 (ADJ)
unnamed: D5.2 (A), L2.2, U20.2 (SW1)
unnamed: D6.1 (K), L3.1, U20.20 (SW2)
unnamed: L2.1, U20.3 (INBK)
unnamed: R57.2, U20.8 (COMP1)
unnamed: R58.2, U20.12 (COMP2)
unnamed: R59.2, R60.1, U20.7 (FB1)
unnamed: R61.2, R62.1, U20.13 (FB2)
unnamed: R63.2, R64.1, U21.4 (SENSE/ADJ)

Notes on the sheet:
ADP5071AREZ (5 V in): +16.5 V boost and -16.5 V inverting rails; ADP7142 (+15 V) and ADP7182 (-15 V) post-regulate.
Values from ADP5071 datasheet Fig. 47 / Tables 9-11 (+/-16.5 V output rows rescaled via RFT). ADP7182 EN tied to VIN (auto-start); |VEN| >= 2 V enables.
ADP5071 DECOUPLING CAPACITORS
