jhyland87/Cryocooler-Controller/hardware/kicad/sheets/rails_logic.kicad_sch

## KiCad design hardware/kicad/sheets/rails_logic.kicad_sch (2026-10-04)

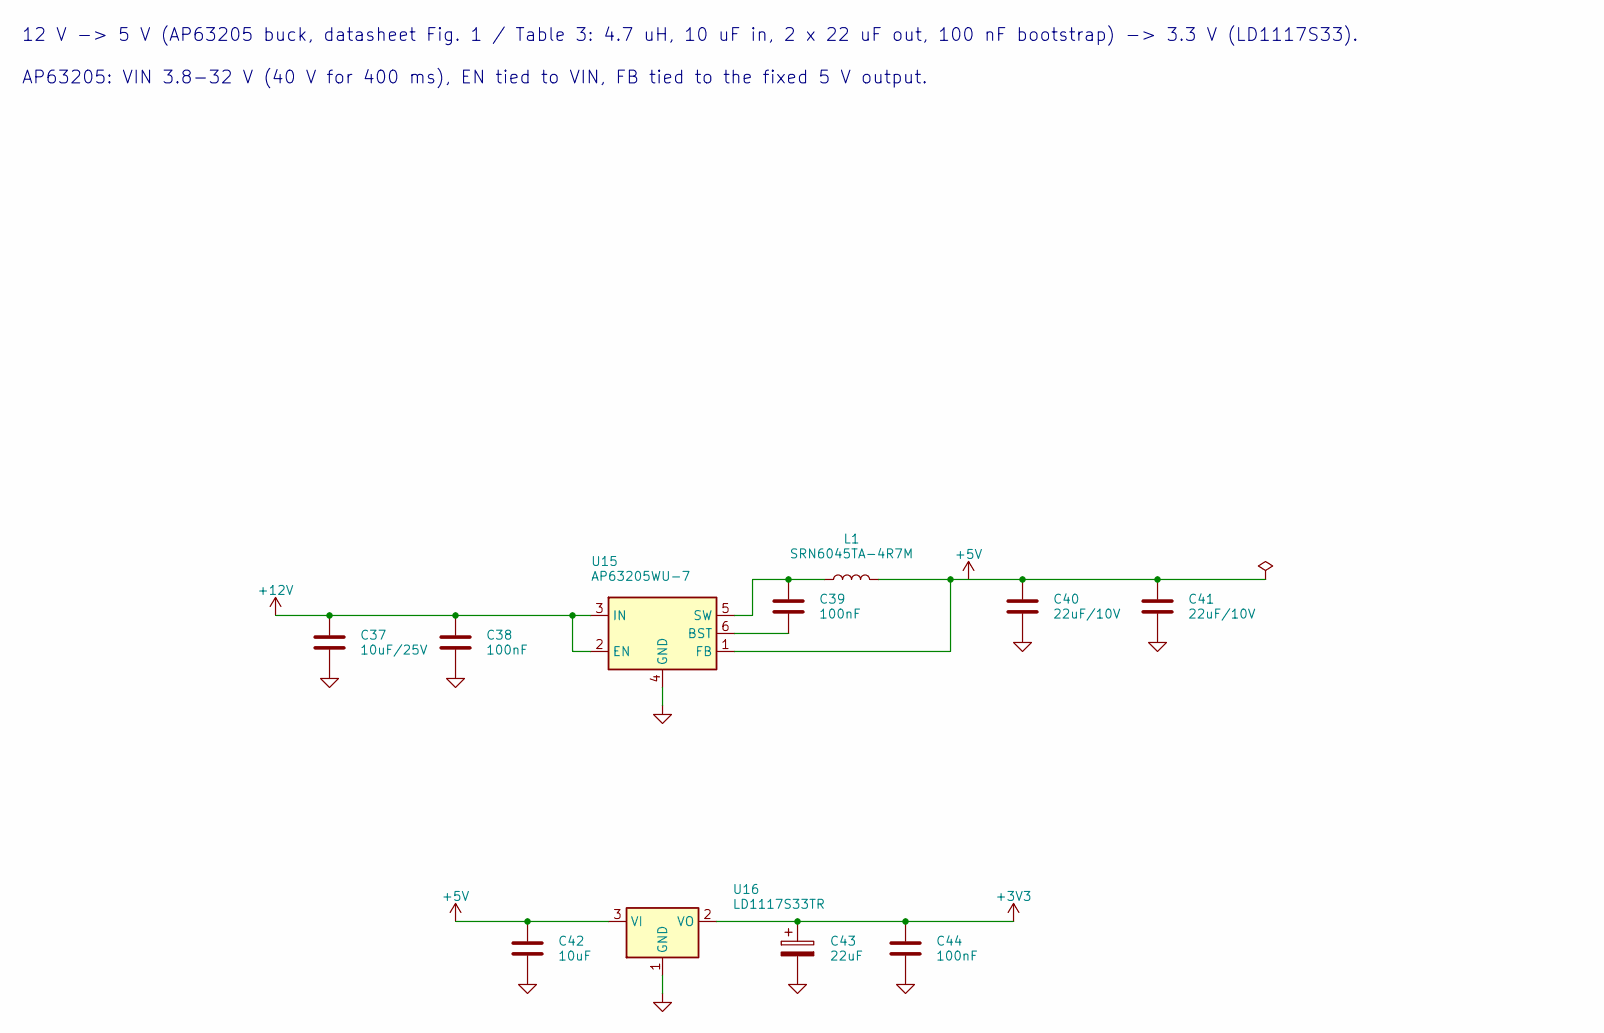
[picture p32: schematic rails_logic.kicad_sch]

Parts:
C37: 10uF/25V; C_1206_3216Metric
C38, C39, C44: 100nF; C_0603_1608Metric
C40, C41: 22uF/10V; C_1206_3216Metric
C42: 10uF; C_0805_2012Metric
C43: 22uF; CP_EIA-3528-21_Kemet-B
L1: SRN6045TA-4R7M; L_Bourns_SRN6045TA
U15: AP63205WU-7; TSOT-23-6
U16: LD1117S33TR; SOT-223-3_TabPin2

Connections:
+3V3: C43.1, C44.1, U16.2 (VO)
+5V: C40.1, C41.1, C42.1, L1.2, U15.1 (FB), U16.3 (VI)
+12V: C37.1, C38.1, U15.2 (EN), U15.3 (IN)
GND: C37.2, C38.2, C40.2, C41.2, C42.2, C43.2, C44.2, U15.4 (GND), U16.1 (GND)
unnamed: C39.1, L1.1, U15.5 (SW)
unnamed: C39.2, U15.6 (BST)

Notes on the sheet:
AP63205: VIN 3.8-32 V (40 V for 400 ms), EN tied to VIN, FB tied to the fixed 5 V output.
12 V -> 5 V (AP63205 buck, datasheet Fig. 1 / Table 3: 4.7 uH, 10 uF in, 2 x 22 uF out, 100 nF bootstrap) -> 3.3 V (LD1117S33).
