jhyland87/Cryocooler-Controller/hardware/kicad/sheets/signal_gen.kicad_sch

## KiCad design hardware/kicad/sheets/signal_gen.kicad_sch (2026-10-04)

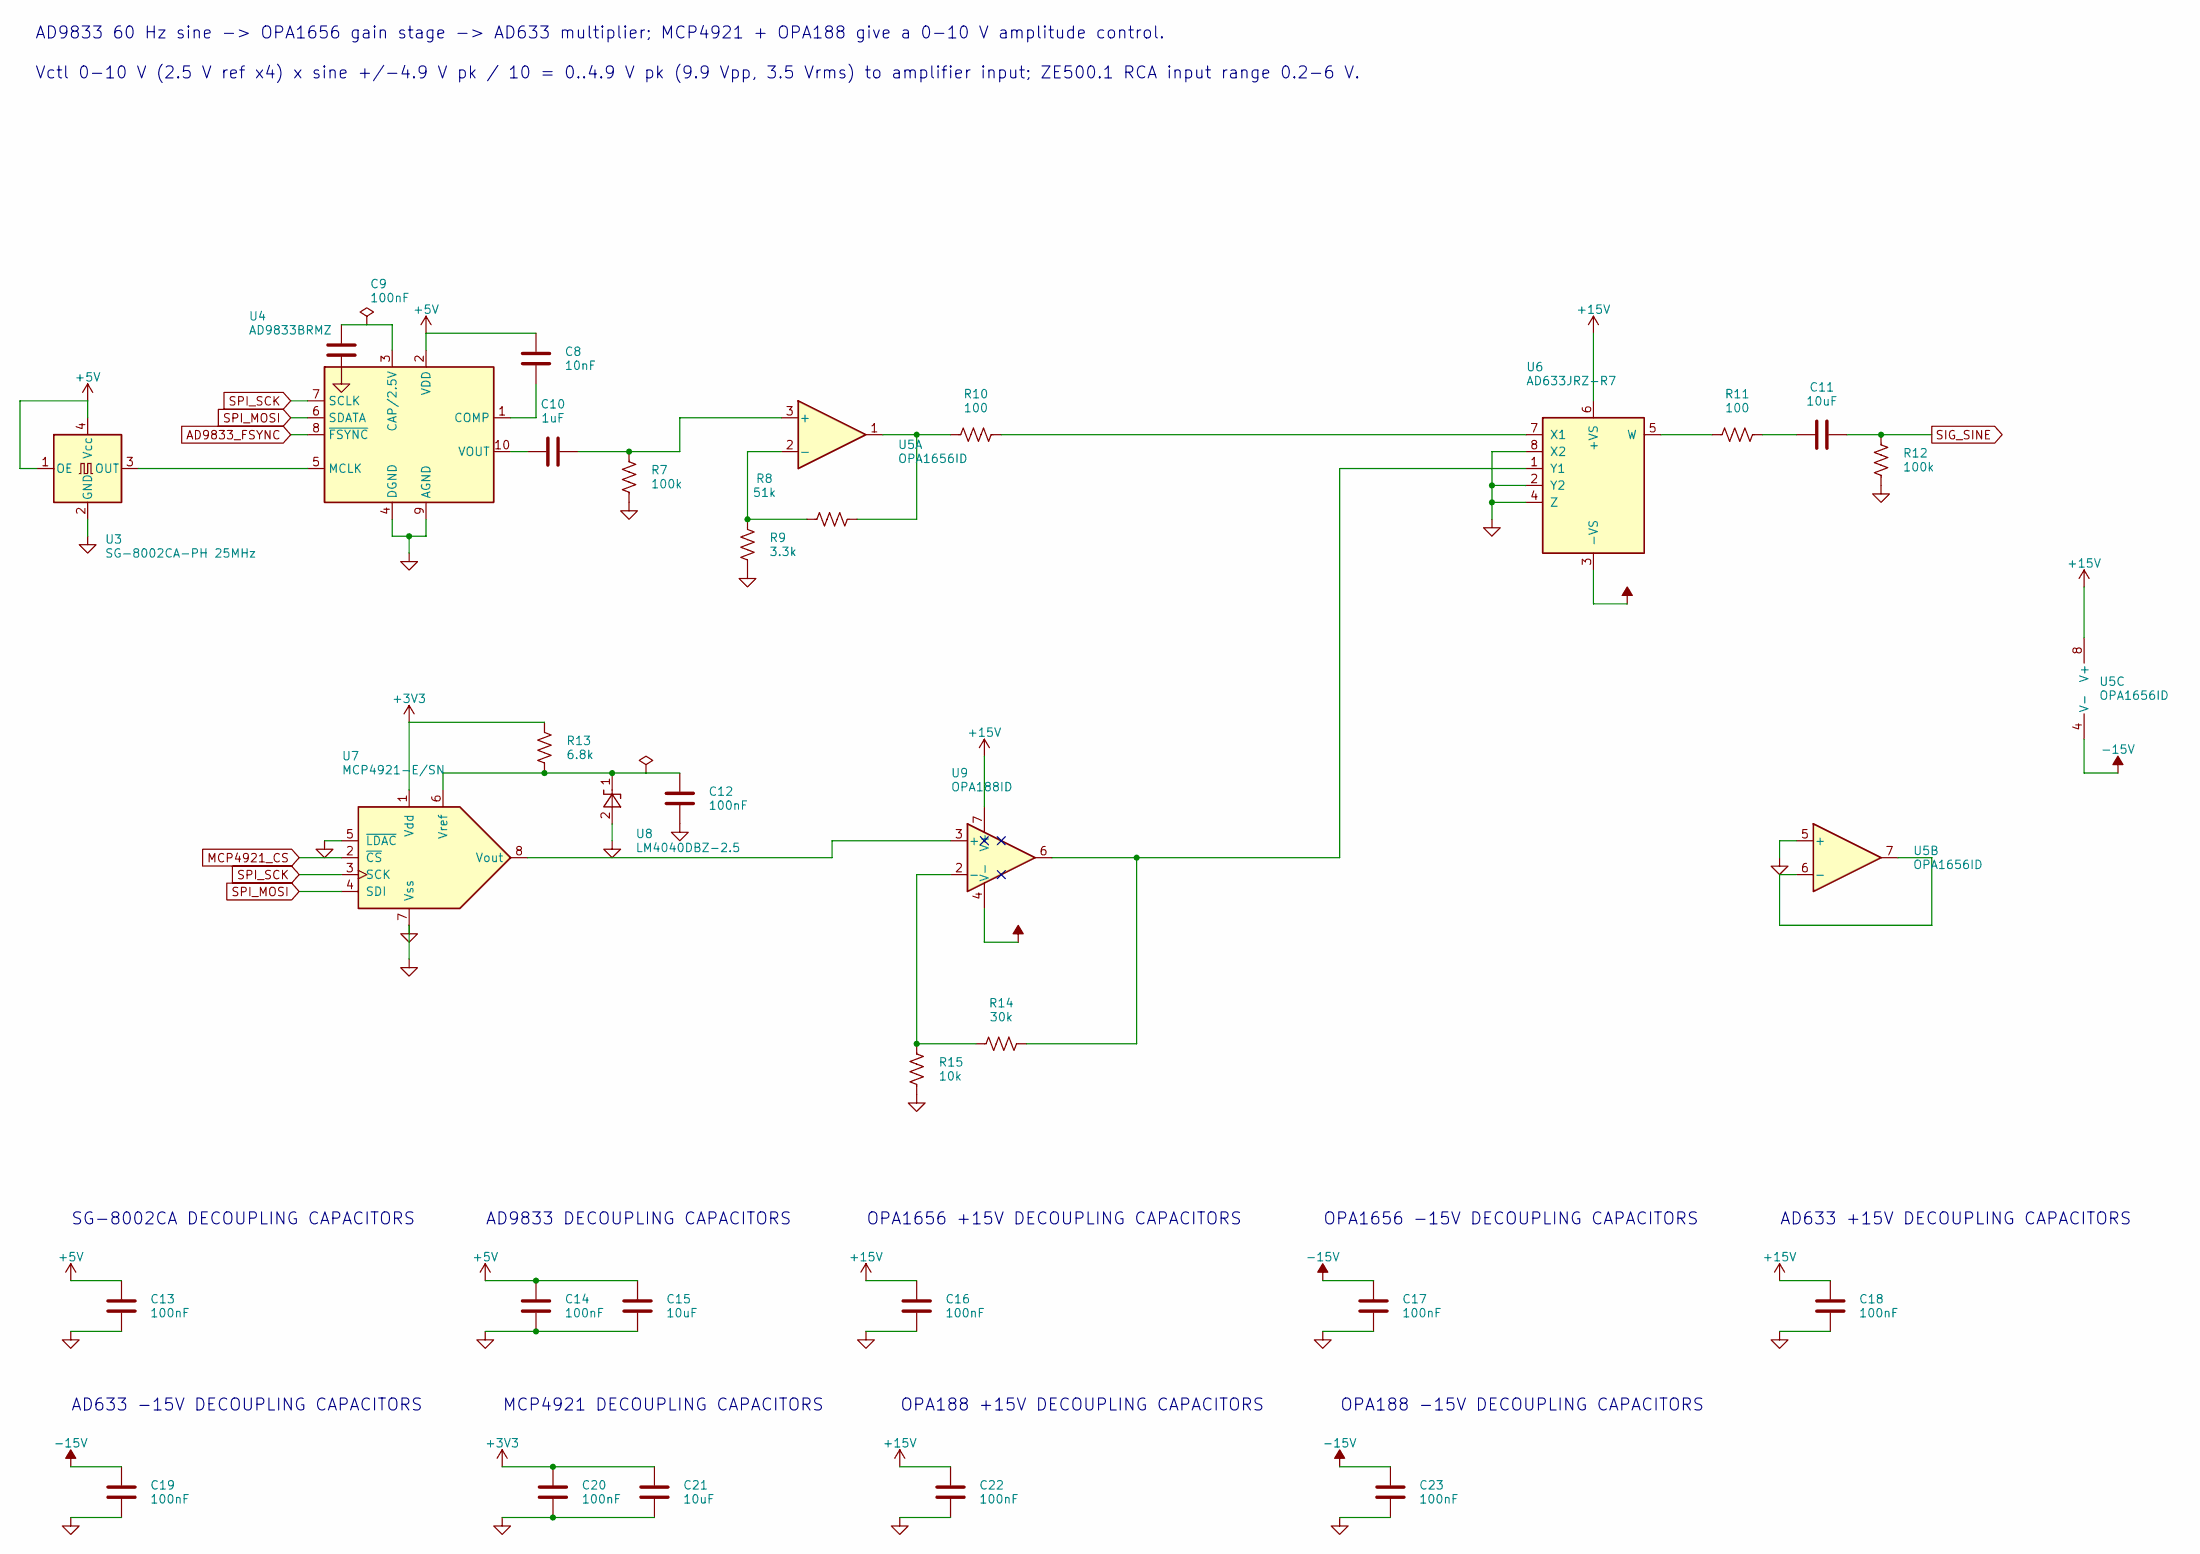
[picture p33: schematic signal_gen.kicad_sch]

Parts:
C8: 10nF; C_0603_1608Metric
C9, C12, C13, C14, C16, C17, C18, C19, C20, C22, C23: 100nF; C_0603_1608Metric
C10: 1uF; C_0805_2012Metric
C11, C15, C21: 10uF; C_0805_2012Metric
R7, R12: 100k; R_0603_1608Metric
R8: 51k; R_0603_1608Metric
R9: 3.3k; R_0603_1608Metric
R10, R11: 100; R_0603_1608Metric
R13: 6.8k; R_0603_1608Metric
R14: 30k; R_0603_1608Metric
R15: 10k; R_0603_1608Metric
U3: SG-8002CA-PH 25MHz; Oscillator_SMD_SeikoEpson_SG8002CA-4Pin_7.0x5.0mm
U4: AD9833BRMZ; MSOP-10_3x3mm_P0.5mm
U5: OPA1656ID; SOIC-8_3.9x4.9mm_P1.27mm
U6: AD633JRZ-R7; SOIC-8_3.9x4.9mm_P1.27mm
U7: MCP4921-E/SN; SOIC-8_3.9x4.9mm_P1.27mm
U8: LM4040DBZ-2.5; SOT-23
U9: OPA188ID; SOIC-8_3.9x4.9mm_P1.27mm

Connections:
+3V3: C20.1, C21.1, R13.1, U7.1 (Vdd)
+5V: C8.1, C13.1, C14.1, C15.1, U3.1 (OE), U3.4 (Vcc), U4.2 (VDD)
+15V: C16.1, C18.1, C22.1, U5.8 (V+), U6.6 (+VS), U9.7 (V+)
-15V: C17.1, C19.1, C23.1, U5.4 (V-), U6.3 (-VS), U9.4 (V-)
AD9833_FSYNC: U4.8 (~FSYNC)
GND: C9.2, C12.2, C13.2, C14.2, C15.2, C16.2, C17.2, C18.2, C19.2, C20.2, C21.2, C22.2, C23.2, R7.2, R9.2, R12.2, R15.2, U3.2 (GND), U4.4 (DGND), U4.9 (AGND), U5.5 (+), U6.2 (Y2), U6.4 (Z), U6.8 (X2), U7.5 (~LDAC), U7.7 (Vss), U8.2 (A)
MCP4921_CS: U7.2 (~CS)
unnamed: C8.2, U4.1 (COMP)
unnamed: C9.1, U4.3 (CAP/2.5V)
unnamed: C10.1, U4.10 (VOUT)
unnamed: C10.2, R7.1, U5.3 (+)
unnamed: C11.1, R11.2
unnamed: C12.1, R13.2, U7.6 (Vref), U8.1 (K)
unnamed: R8.1, R9.1, U5.2 (-)
unnamed: R8.2, R10.1, U5.1
unnamed: R10.2, U6.7 (X1)
unnamed: R11.1, U6.5 (W)
unnamed: R14.1, R15.1, U9.2 (-)
unnamed: R14.2, U6.1 (Y1), U9.6
unnamed: U3.3 (OUT), U4.5 (MCLK)
unnamed: U5.6 (-), U5.7
unnamed: U7.8 (Vout), U9.3 (+)
SIG_SINE: C11.2, R12.1
SPI_MOSI: U4.6 (SDATA), U7.4 (SDI)
SPI_SCK: U4.7 (SCLK), U7.3 (SCK)

Notes on the sheet:
Vctl 0-10 V (2.5 V ref x4) x sine +/-4.9 V pk / 10 = 0..4.9 V pk (9.9 Vpp, 3.5 Vrms) to amplifier input; ZE500.1 RCA input range 0.2-6 V.
OPA188 -15V DECOUPLING CAPACITORS
AD633 -15V DECOUPLING CAPACITORS
AD9833 60 Hz sine -> OPA1656 gain stage -> AD633 multiplier; MCP4921 + OPA188 give a 0-10 V amplitude control.
OPA1656 +15V DECOUPLING CAPACITORS
AD633 +15V DECOUPLING CAPACITORS
OPA188 +15V DECOUPLING CAPACITORS
OPA1656 -15V DECOUPLING CAPACITORS
AD9833 DECOUPLING CAPACITORS
SG-8002CA DECOUPLING CAPACITORS
MCP4921 DECOUPLING CAPACITORS
