jhyland87/Cryocooler-Controller/hardware/kicad/sheets/system_current.kicad_sch

## KiCad design hardware/kicad/sheets/system_current.kicad_sch (2026-10-04)

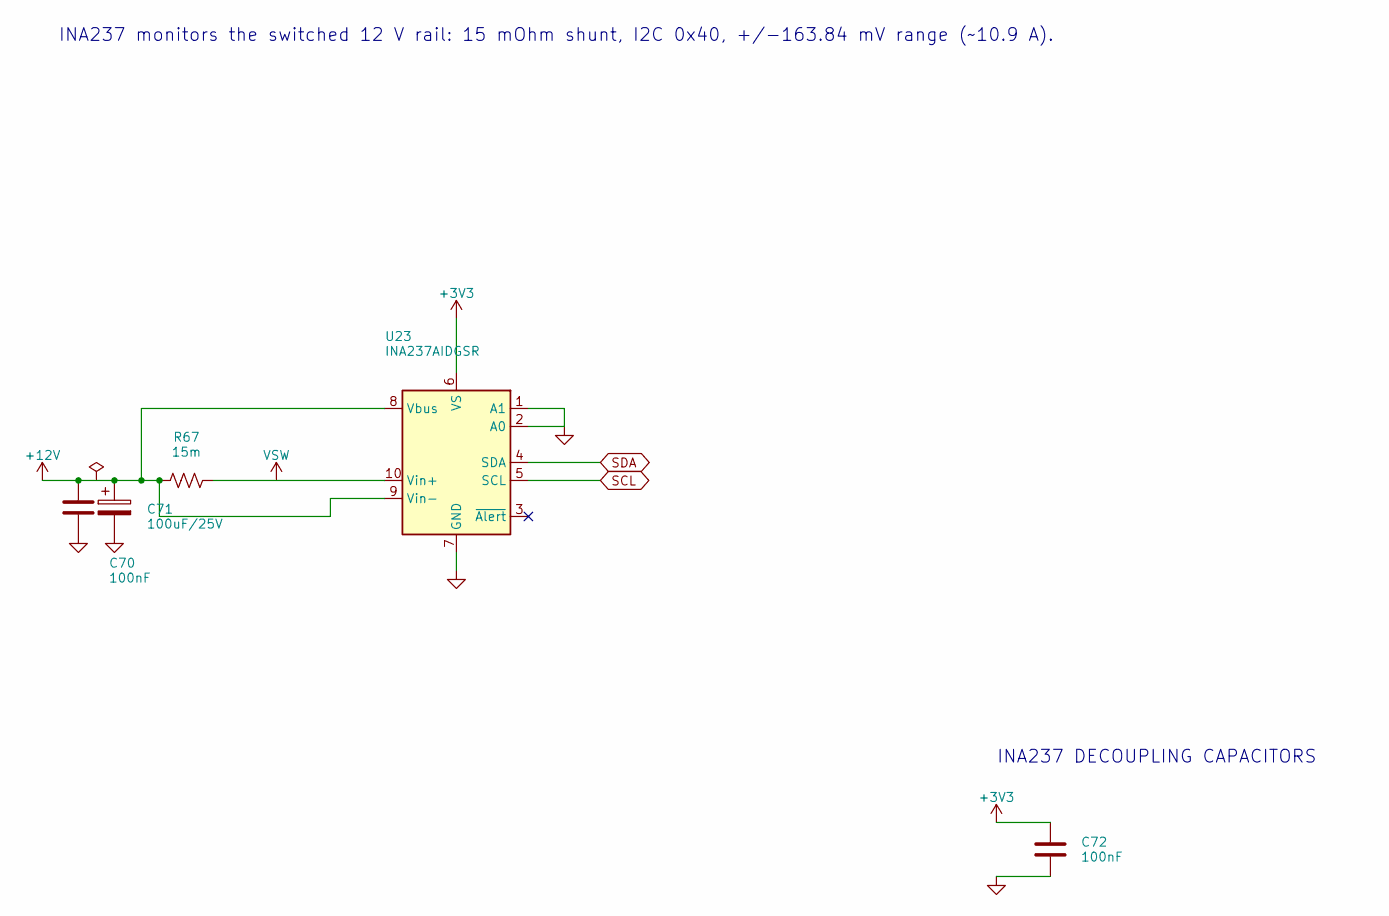
[picture p34: schematic system_current.kicad_sch]

Parts:
C70: 100nF; C_0805_2012Metric
C71: 100uF/25V; CP_Elec_8x10
C72: 100nF; C_0603_1608Metric
R67: 15m; R_2512_6332Metric
U23: INA237AIDGSR; TSSOP-10_3x3mm_P0.5mm

Connections:
+3V3: C72.1, U23.6 (VS)
+12V: C70.1, C71.1, R67.1, U23.8 (Vbus), U23.9 (Vin-)
GND: C70.2, C71.2, C72.2, U23.1 (A1), U23.2 (A0), U23.7 (GND)
SCL: U23.5 (SCL)
SDA: U23.4 (SDA)
VSW: R67.2, U23.10 (Vin+)

Notes on the sheet:
INA237 monitors the switched 12 V rail: 15 mOhm shunt, I2C 0x40, +/-163.84 mV range (~10.9 A).
INA237 DECOUPLING CAPACITORS
