jhyland87/Cryocooler-Controller/hardware/kicad/sim/cryocooler_sim.kicad_sch

## KiCad design hardware/kicad/sim/cryocooler_sim.kicad_sch (2026-10-04)

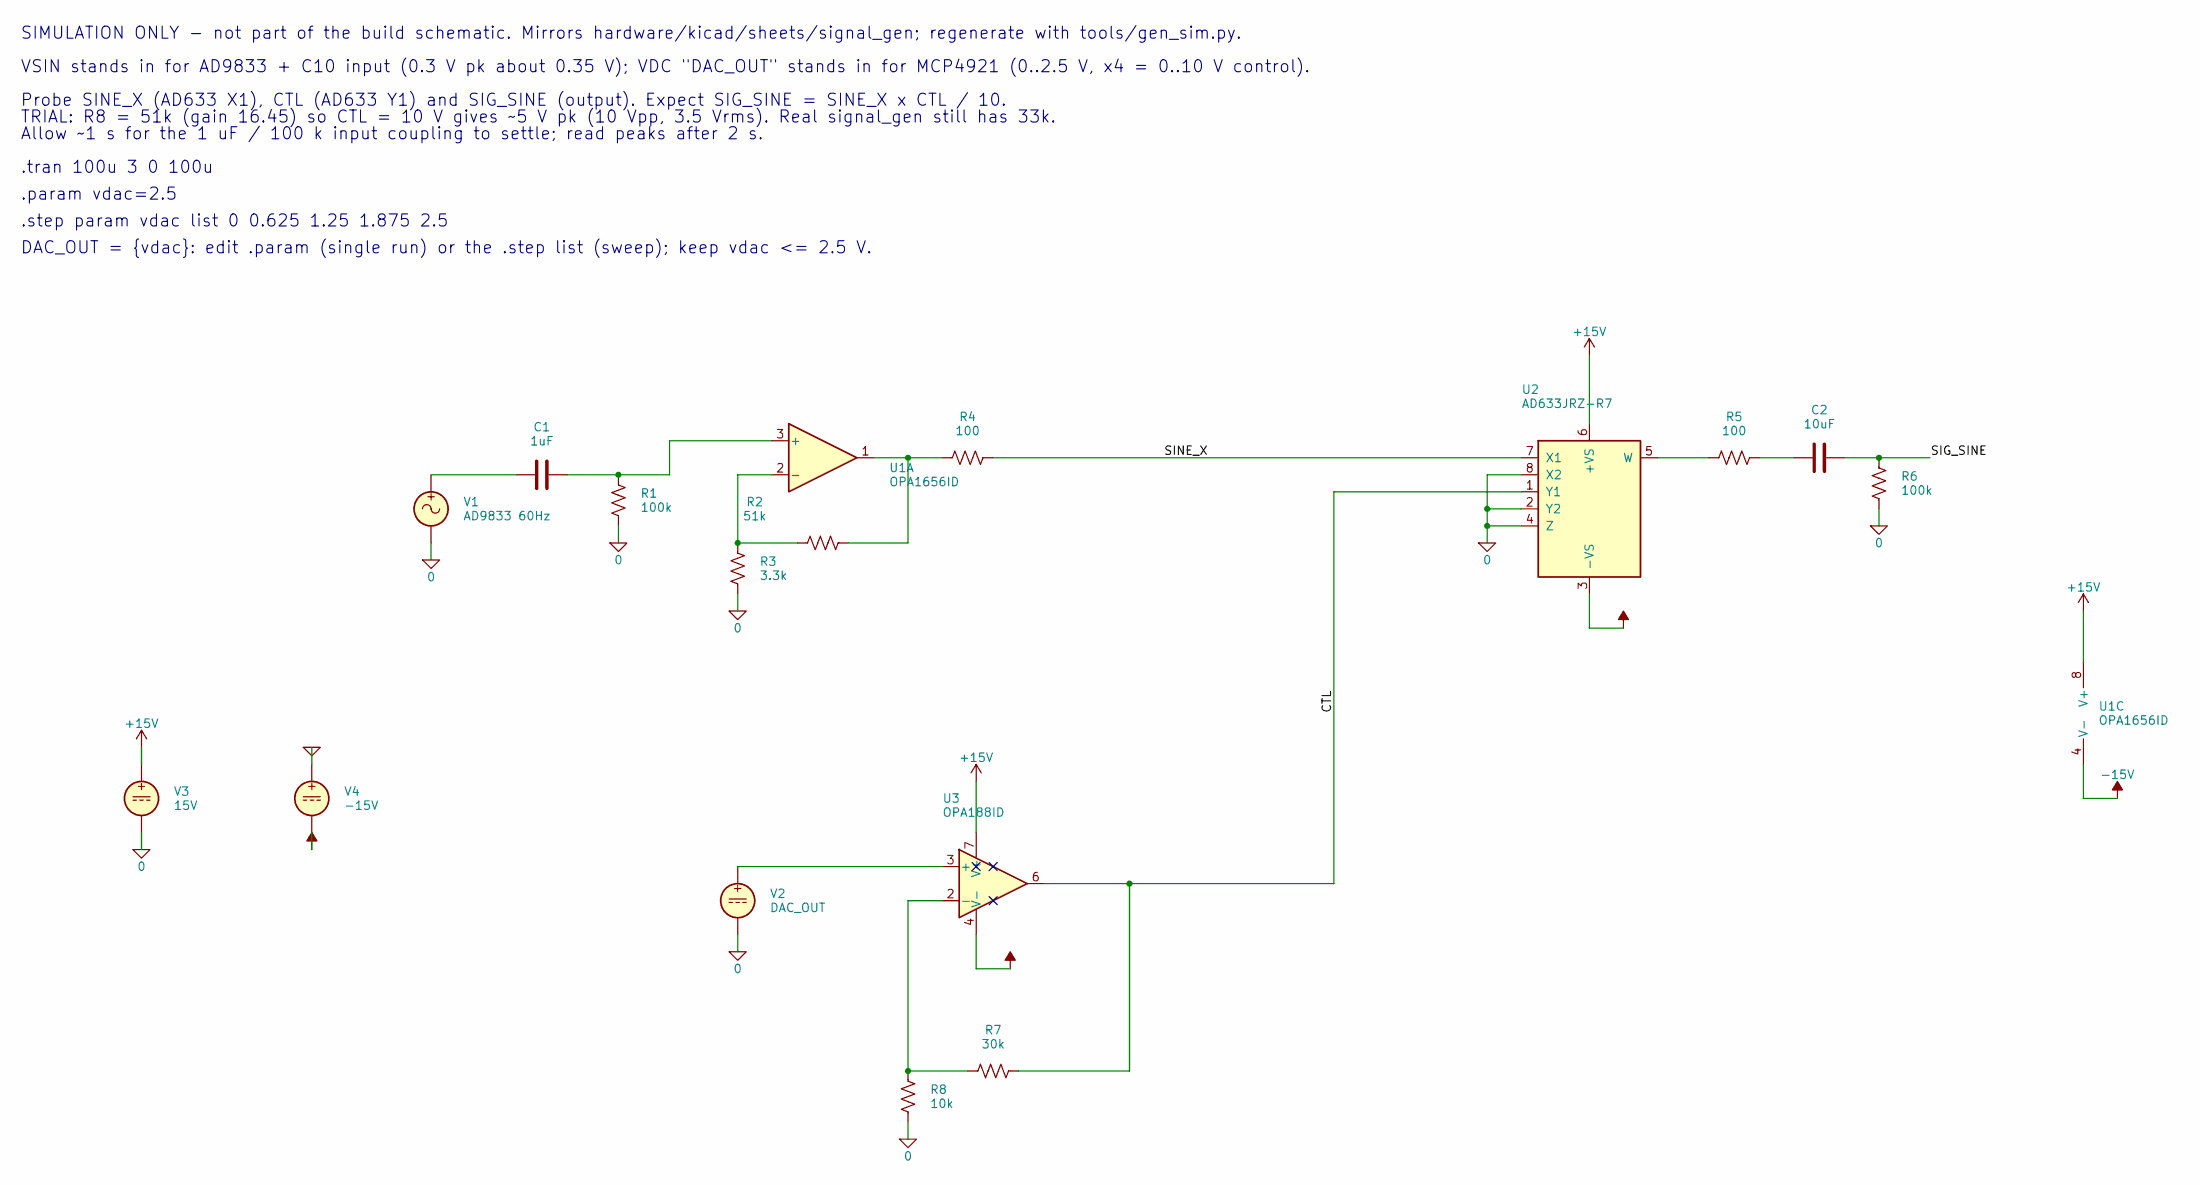
[picture p35: schematic cryocooler_sim.kicad_sch]

Parts:
C1: 1uF; C_0805_2012Metric
C2: 10uF; C_0805_2012Metric
R1, R6: 100k; R_0603_1608Metric
R2: 51k; R_0603_1608Metric
R3: 3.3k; R_0603_1608Metric
R4, R5: 100; R_0603_1608Metric
R7: 30k; R_0603_1608Metric
R8: 10k; R_0603_1608Metric
U1: OPA1656ID; SOIC-8_3.9x4.9mm_P1.27mm
U2: AD633JRZ-R7; SOIC-8_3.9x4.9mm_P1.27mm
U3: OPA188ID; SOIC-8_3.9x4.9mm_P1.27mm
V1: AD9833 60Hz
V2: DAC_OUT
V3: 15V
V4: -15V

Connections:
0: R1.2, R3.2, R6.2, R8.2, U2.2 (Y2), U2.4 (Z), U2.8 (X2), V1.2, V2.2, V3.2, V4.1
+15V: U1.8 (V+), U2.6 (+VS), U3.7 (V+), V3.1
-15V: U1.4 (V-), U2.3 (-VS), U3.4 (V-), V4.2
CTL: R7.2, U2.1 (Y1), U3.6
unnamed: C1.1, V1.1
unnamed: C1.2, R1.1, U1.3 (+)
unnamed: C2.1, R5.2
unnamed: R2.1, R3.1, U1.2 (-)
unnamed: R2.2, R4.1, U1.1
unnamed: R5.1, U2.5 (W)
unnamed: R7.1, R8.1, U3.2 (-)
unnamed: U3.3 (+), V2.1
SIG_SINE: C2.2, R6.1
SINE_X: R4.2, U2.7 (X1)

Notes on the sheet:
Probe SINE_X (AD633 X1), CTL (AD633 Y1) and SIG_SINE (output). Expect SIG_SINE = SINE_X x CTL / 10.
.tran 100u 3 0 100u
.param vdac=2.5
Allow ~1 s for the 1 uF / 100 k input coupling to settle; read peaks after 2 s.
.step param vdac list 0 0.625 1.25 1.875 2.5
DAC_OUT = {vdac}: edit .param (single run) or the .step list (sweep); keep vdac <= 2.5 V.
SIMULATION ONLY - not part of the build schematic. Mirrors hardware/kicad/sheets/signal_gen; regenerate with tools/gen_sim.py.
VSIN stands in for AD9833 + C10 input (0.3 V pk about 0.35 V); VDC "DAC_OUT" stands in for MCP4921 (0..2.5 V, x4 = 0..10 V control).
TRIAL: R8 = 51k (gain 16.45) so CTL = 10 V gives ~5 V pk (10 Vpp, 3.5 Vrms). Real signal_gen still has 33k.
