jhyland87/Cryocooler-Controller/src/commands.cpp

/**
 * @file commands.cpp
 * @brief Generic command dispatcher — sources: Serial, TCP (Serial Studio), etc.
 *
 * processLine() is transport-agnostic: it accepts any Print& as the response
 * sink, so the same command table works for serial input and TCP input.
 *
 * service() handles the Serial-specific accumulation (non-blocking).
 * The TCP path calls processLine() directly from the AsyncTCP data callback.
 */

#ifdef ARDUINO
#  include <Arduino.h>
#else
#  include <cstdio>
#  include <cstring>
#  include <cctype>
#  include "Arduino.h"  // native stub — provides millis() and Print
#endif

#include "commands.h"
#include "conversions.h"
#include "state_machine.h"
#include "state_machine_history.h"
#include "telemetry.h"
#include "cold_head.h"
//#include "rms.h"
//#include "dac.h"
#include "indicator.h"
#include "cooling.h"
#include "config.h"
#ifdef ARDUINO
#include <WiFi.h>
#include <esp_ota_ops.h>  // esp_app_desc_t lives here on IDF 5.1.x
#include "dashboard.h"
#include "mock_commands.h"
#include "amplifier.h"
#include "sensor_mock.h"
#include "ota.h"
#include "compressor.h"
#include "utils.h"
#include "hardware.h"
#include "imu.h"
#include "sysinfo.h"
#include "espnow.h"
#endif
#include "logger.h"

namespace commands {

// ─── Line buffer (serial accumulator) ────────────────────────────────────────

static constexpr uint8_t  maxLineLen       = 80;
static constexpr uint32_t commandTimeoutMs = 100;  ///< dispatch after this many ms with no new byte

static char     lineBuf[maxLineLen + 1];
static uint8_t  lineLen    = 0;
static uint32_t lastCharMs = 0;  ///< millis() of the most recently buffered printable byte

#ifdef ARDUINO
// ─── OTA confirmation state ───────────────────────────────────────────────────
//
// 'update image' sets this flag and prompts the user to type 'yes'.
// processLine() intercepts the next non-empty input while the flag is set:
//   • "yes" → print the OTA URL and arm the endpoint
//   • anything else → cancel and reset
//
// The flag is per-session (not persisted across reboots).

static bool s_awaitingUpdateConfirm = false;
#endif

// ─── Command handler type and dispatch table ──────────────────────────────────

// args: everything after the command name (leading whitespace stripped).
// Empty string ("") when no argument was provided.
using HandlerFn = void (*)(const char* args, Print& out);

struct Command {
    const char* name;
    HandlerFn   handler;
    const char* help;
};

// Forward declaration so handleHelp can reference commands[] below.
static void handleHelp(const char* args, Print& out);

// ─── Individual command handlers ──────────────────────────────────────────────

static void handleStart(const char* /*args*/, Print& out) {
    if (state_machine::isRunning()) {
        out.println(F("[ERR] Already running"));
        return;
    }
    if (state_machine::getState() != state_machine::State::Idle &&
        state_machine::getState() != state_machine::State::Off) {
        out.println(F("[ERR] Cannot start: not in Idle or Off state"));
        return;
    }

#ifdef ARDUINO
    // Use mock temperature when active so the FSM picks the right entry
    // state (coarse vs fine vs settle) even without real hardware.
    const float tempC = sensor_mock::isActive()
                            ? sensor_mock::get().tempC
                            : cold_head::getLastTempC();
    state_machine::start(tempC);
#else
    state_machine::start();
#endif
    out.println(F("[OK] Process started"));
}

#ifdef ARDUINO

/**
 * Helper: check if a whitespace-delimited token list contains a given name.
 * Returns true if `name` appears as an exact whitespace-separated token in `args`.
 */
static bool argsContain(const char* args, const char* name) {
    const size_t nameLen = strlen(name);
    const char* p = args;
    while (*p) {
        while (*p == ' ' || *p == '\t') ++p;
        if (*p == '\0') break;
        const char* start = p;
        while (*p && *p != ' ' && *p != '\t') ++p;
        if (static_cast<size_t>(p - start) == nameLen &&
            strncmp(start, name, nameLen) == 0) {
            return true;
        }
    }
    return false;
}

static void handleReinit(const char* args, Print& out) {
    // Allow reinit only from safe non-running states.  If the process is
    // actively running the operator should stop it first to allow a clean
    // shutdown ramp before re-initialising hardware.
    // Initialize is also allowed so a failed startup (stuck in Initialize
    // because a hardware module was missing) can be retried without having
    // to issue an 'off' command first.
    const auto s = state_machine::getState();
    if (s != state_machine::State::Off        &&
        s != state_machine::State::Idle       &&
        s != state_machine::State::Initialize &&
        s != state_machine::State::Fault) {
        char buf[80];
        snprintf(buf, sizeof(buf),
                 "[ERR] Cannot reinit while in %s — stop the system first",
                 state_machine::stateName(s));
        out.println(buf);
        return;
    }

    // If no arguments, do a full reinit (all control modules via the FSM).
    if (*args == '\0') {
        state_machine::reinit();
        char buf[72];
        snprintf(buf, sizeof(buf), "[OK] Reinitializing all — state: %s | mock: %s",
                 state_machine::stateName(state_machine::getState()),
                 sensor_mock::isActive() ? "ACTIVE" : "inactive");
        out.println(buf);
        return;
    }

    // ── Selective reinit: re-initialise only the named module(s) ─────────
    // Accepted names match the module namespaces used throughout the system.

    struct SelectiveModule {
        const char* name;
        module::InitStatus (*initFn)();
    };

    const SelectiveModule selectableModules[] = {
        { "amplifier",  [] () -> module::InitStatus { return amplifier::Module::init(); }  },
        { "cooling",    [] () -> module::InitStatus { return cooling::Module::init(); }    },
        { "cold_head",  [] () -> module::InitStatus { return cold_head::Module::init(); }  },
#if ENABLE_COMPRESSOR
        { "compressor", [] () -> module::InitStatus { return compressor::Module::init(); } },
#endif
        { "imu",        [] () -> module::InitStatus { return imu::Module::init(); }        },
        { "dashboard",  [] () -> module::InitStatus { return dashboard::Module::init(); }  },
        { "indicator",  [] () -> module::InitStatus { return indicator::Module::init(); }   },
        { "ota",        [] () -> module::InitStatus { return ota::Module::init(); }         },
        { "sysinfo",    [] () -> module::InitStatus { return sysinfo::Module::init(); }     },
        { "hardware",   [] () -> module::InitStatus { return hardware::Module::init(); }    },
#if ENABLE_ESPNOW
        { "espnow",     [] () -> module::InitStatus { return espnow::Module::init(); }     },
#endif
    };

    uint8_t reinitCount = 0;
    for (const auto& m : selectableModules) {
        if (!argsContain(args, m.name)) continue;

        const auto status = m.initFn();
        char buf[80];
        snprintf(buf, sizeof(buf), "  %-14s  %s",
                 m.name, module::initStatusName(status));
        out.println(buf);
        ++reinitCount;
    }

    if (reinitCount == 0) {
        out.println(F("[ERR] No valid module names found. Available:"));
        for (const auto& m : selectableModules) {
            char buf[32];
            snprintf(buf, sizeof(buf), "  %s", m.name);
            out.println(buf);
        }
    } else {
        char buf[48];
        snprintf(buf, sizeof(buf), "[OK] Reinitialized %u module(s)", reinitCount);
        out.println(buf);
    }
}
#endif

static void handleStop(const char* /*args*/, Print& out) {
    if (state_machine::getState() == state_machine::State::Fault) {
        // Defer the stop — will suppress auto-start on next fault clear.
        state_machine::stop();
        out.println(F("[OK] Stop deferred — will take effect on fault clear"));
        return;
    }
    if (!state_machine::isRunning()) {
        out.println(F("[ERR] Not currently running"));
        return;
    }
    state_machine::stop();
    out.println(F("[OK] Process stopped"));
}

static void handleReboot(const char* /*args*/, Print& out) {
    out.println(F("[OK] Rebooting requested..."));
#ifdef ARDUINO
    ESP.restart();
#endif
    out.println(F("[OK] System rebooted"));
}

static void handleOff(const char* /*args*/, Print& out) {
    if (state_machine::getState() == state_machine::State::Off) {
        out.println(F("[ERR] System is already off"));
        return;
    }
    state_machine::off();
    out.println(F("[OK] System turned off"));
}

static void handleStatus(const char* /*args*/, Print& out) {
    char buf[96];
    snprintf(buf, sizeof(buf), "[OK] %s (%d) | running: %s",
             state_machine::stateName(state_machine::getState()),
             static_cast<int8_t>(state_machine::getState()),
             state_machine::isRunning() ? "yes" : "no");
    out.println(buf);

#ifdef ARDUINO
    // ── Module status table ──────────────────────────────────────────────────
    // Show init and service status for every registered module so the
    // operator can quickly see which subsystems are healthy.
    out.println(F("  Module status:"));

    struct ModuleInfo {
        const char*          name;
        module::InitStatus    init;
        module::ServiceStatus svc;
    };

    const ModuleInfo modules[] = {
        { "hardware",    hardware::Module::getInitStatus(),    hardware::Module::getServiceStatus()    },
        { "indicator",   indicator::Module::getInitStatus(),   indicator::Module::getServiceStatus()   },
        { "ota",         ota::Module::getInitStatus(),         ota::Module::getServiceStatus()         },
        { "dashboard",   dashboard::Module::getInitStatus(),   dashboard::Module::getServiceStatus()   },
        { "telemetry",   telemetry::Module::getInitStatus(),   telemetry::Module::getServiceStatus()   },
        { "sysinfo",     sysinfo::Module::getInitStatus(),     sysinfo::Module::getServiceStatus()     },
        { "imu",         imu::Module::getInitStatus(),         imu::Module::getServiceStatus()         },
        { "amplifier",   amplifier::Module::getInitStatus(),   amplifier::Module::getServiceStatus()   },
        { "cooling",     cooling::Module::getInitStatus(),     cooling::Module::getServiceStatus()     },
        { "cold_head",   cold_head::Module::getInitStatus(),   cold_head::Module::getServiceStatus()   },
#if ENABLE_COMPRESSOR
        { "compressor",  compressor::Module::getInitStatus(),  compressor::Module::getServiceStatus()  },
#endif
#if ENABLE_ESPNOW
        { "espnow",      espnow::Module::getInitStatus(),      espnow::Module::getServiceStatus()      },
#endif
        { "state_machine", state_machine::Module::getInitStatus(), state_machine::Module::getServiceStatus() },
    };

    for (const auto& m : modules) {
        char line[80];
        snprintf(line, sizeof(line), "    %-14s  init: %-16s  svc: %s",
                 m.name,
                 module::initStatusName(m.init),
                 module::serviceStatusName(m.svc));
        out.println(line);
    }
#endif
    out.println("");
}

static void handleTelemetryOff(const char* /*args*/, Print& out) {
    telemetry::disable();
#ifdef ARDUINO
    // Also silence the TCP dashboard stream — both transports carry telemetry.
    // Use `dashboard on` to re-enable the TCP stream independently if needed.
    dashboard::disable();
#endif
    out.println(F("[OK] Telemetry disabled"));
}

static void handleTelemetryOn(const char* /*args*/, Print& out) {
    telemetry::enable();
#ifdef ARDUINO
    dashboard::enable();
#endif
    out.println(F("[OK] Telemetry enabled"));
}

static void handleTelemetryDeltaOff(const char* /*args*/, Print& out) {
    telemetry::disableDelta();
    out.println(F("[OK] Telemetry delta mode disabled (full frame each emit)"));
}

static void handleTelemetryDeltaOn(const char* /*args*/, Print& out) {
    telemetry::enableDelta();
    out.println(F("[OK] Telemetry delta mode enabled (only changed values emitted)"));
}

#ifdef ARDUINO
static void handleDashboardOff(const char* /*args*/, Print& out) {
    dashboard::disable();
    out.println(F("[OK] Dashboard disabled"));
}

static void handleDashboardOn(const char* /*args*/, Print& out) {
    dashboard::enable();
    out.println(F("[OK] Dashboard enabled"));
}
#endif


static void handleCoolingOn(const char* /*args*/, Print& out) {
    cooling::enable();
    out.println(F("[OK] Cooling enabled"));
}

static void handleCoolingOff(const char* /*args*/, Print& out) {
    cooling::disable();
    out.println(F("[OK] Cooling disabled"));
}

#ifdef ARDUINO
static void handleVoutGet(const char* /*args*/, Print& out) {
    uint16_t val = amplifier::getLastRmsVoltage();
    char buf[48];
    snprintf(buf, sizeof(buf), "[OK] Voltage set to %uV", static_cast<unsigned>(val));
    out.println(buf);
}

static void handleVoutSet(const char* args, Print& out) {
    if (*args == '\0') {
        out.println(F("[ERR] Usage: set vout <0-120V> | <0-100%> | auto"));
        return;
    }

    // "auto" clears the manual override and resumes FSM-driven output.
    if (strncmp(args, "auto", 4) == 0 &&
        (args[4] == '\0' || args[4] == ' ' || args[4] == '\t')) {
        amplifier::clearVoutOverride();
        out.println(F("[OK] Vout override cleared — resumed FSM control"));
        return;
    }

    // Parse up to 4 digits (anything ≥ 1000 will fail the range check).
    uint16_t val    = 0;
    uint8_t  digits = 0;
    const char* p = args;
    while (*p >= '0' && *p <= '9' && digits < 4u) {
        val = static_cast<uint16_t>(val * 10u + static_cast<uint16_t>(*p - '0'));
        ++p;
        ++digits;
    }

    // Reject if no digits were found.
    if (digits == 0) {
        char buf[64];
        snprintf(buf, sizeof(buf),
                 "[ERR] vout set: invalid argument '%s' (expected 0-120V or 0-100%%)", args);
        out.println(buf);
        return;
    }

    // Check for an optional trailing '%' to select percent mode.
    const bool isPercent = (*p == '%');
    if (isPercent) {
        ++p;  // advance past '%'
    }

    // Reject trailing non-whitespace garbage after the value (or after '%').
    if (*p != '\0' && *p != ' ' && *p != '\t') {
        char buf[64];
        snprintf(buf, sizeof(buf),
                 "[ERR] vout set: invalid argument '%s' (expected 0-120V or 0-100%%)", args);
        out.println(buf);
        return;
    }

    if (isPercent) {
        if (val > 100u) {
            char buf[64];
            snprintf(buf, sizeof(buf),
                     "[ERR] vout set: percent out of range '%u%%' (expected 0-100%%)",
                     static_cast<unsigned>(val));
            out.println(buf);
            return;
        }
        const float fraction = static_cast<float>(val) / 100.0f;
        amplifier::setOutput(fraction);
        amplifier::setVoutOverride(fraction);
        char buf[48];
        snprintf(buf, sizeof(buf), "[OK] Voltage set to %u%%", static_cast<unsigned>(val));
        out.println(buf);
    } else {
        if (val > static_cast<uint16_t>(AMPLIFIER_MAX_VOLTAGE_VAC)) {
            char buf[64];
            snprintf(buf, sizeof(buf),
                     "[ERR] vout set: voltage out of range '%uV' (expected 0-%uV)",
                     static_cast<unsigned>(val),
                     static_cast<unsigned>(AMPLIFIER_MAX_VOLTAGE_VAC));
            out.println(buf);
            return;
        }
        const float fraction = static_cast<float>(val) / AMPLIFIER_MAX_VOLTAGE_VAC;
        amplifier::setOutput(fraction);
        amplifier::setVoutOverride(fraction);
        char buf[48];
        snprintf(buf, sizeof(buf), "[OK] Voltage set to %uV", static_cast<unsigned>(val));
        out.println(buf);
    }
}
#endif // ARDUINO — handleVoutGet / handleVoutSet

// Raw SPI DAC write — bypasses all firmware DAC management.
// Identical to the working test sketch: re-inits SPI, toggles CS manually.
// Usage: "dac raw <0-4095>"
static void handleDacRaw(const char* args, Print& out) {
    if (*args == '\0') {
        out.println(F("[ERR] Usage: dac raw <0-4095>"));
        return;
    }
    const uint16_t val = static_cast<uint16_t>(strtoul(args, nullptr, 10));
    if (val > 4095) {
        out.println(F("[ERR] Value must be 0-4095"));
        return;
    }

    // Exactly replicate the test sketch setup
    SPI.end();
    pinMode(MCP4921_CS, OUTPUT);
    digitalWrite(MCP4921_CS, HIGH);
    SPI.begin(SPI_CLK, SPI_MISO, SPI_MOSI, -1);

    const uint16_t cmd = 0x3000 | (val & 0x0FFF);
    SPI.beginTransaction(SPISettings(8000000, MSBFIRST, SPI_MODE0));
    digitalWrite(MCP4921_CS, LOW);
    SPI.transfer16(cmd);
    digitalWrite(MCP4921_CS, HIGH);
    SPI.endTransaction();

    char buf[64];
    snprintf(buf, sizeof(buf), "[OK] Raw SPI write: cmd=0x%04X (val=%u, %.2fV)",
             cmd, val, val * 3.3f / 4095.0f);
    out.println(buf);
}

static void handleCoolingFan(const char* args, Print& out) {
    if (*args == '\0') {
        out.println(F("[ERR] Usage: cooling fan <0-255> | <0-100%>"));
        out.println(F("       Plain number  = raw duty cycle (0-255)"));
        out.println(F("       With '%'      = fan speed 0-100%%"));
        out.println(F("       'cooling on'  = restore LUT control"));
        return;
    }

    // Parse up to 4 digits.
    uint16_t val    = 0;
    uint8_t  digits = 0;
    const char* p = args;
    while (*p >= '0' && *p <= '9' && digits < 4u) {
        val = static_cast<uint16_t>(val * 10u + static_cast<uint16_t>(*p - '0'));
        ++p;
        ++digits;
    }

    if (digits == 0) {
        char buf[64];
        snprintf(buf, sizeof(buf),
                 "[ERR] cooling fan: invalid argument '%s' (expected <duty> or <%%>)", args);
        out.println(buf);
        return;
    }

    // Check for optional trailing '%' to select percent mode.
    const bool isPercent = (*p == '%');
    if (isPercent) { ++p; }

    // Reject trailing non-whitespace garbage.
    if (*p != '\0' && *p != ' ' && *p != '\t') {
        char buf[64];
        snprintf(buf, sizeof(buf),
                 "[ERR] cooling fan: invalid argument '%s' (expected <duty> or <%%>)", args);
        out.println(buf);
        return;
    }

    if (isPercent) {
        if (val > 100u) {
            out.println(F("[ERR] cooling fan: percentage must be 0-100"));
            return;
        }
        cooling::setFanSpeed(static_cast<uint8_t>(val), true);
        char buf[48];
        snprintf(buf, sizeof(buf), "[OK] Fan speed set to %u%% (LUT disabled)",
                 static_cast<unsigned>(val));
        out.println(buf);
    } else {
        if (val > 255u) {
            out.println(F("[ERR] cooling fan: duty cycle must be 0-255"));
            return;
        }
        cooling::setFanDutyCycle(static_cast<uint8_t>(val));
        char buf[48];
        snprintf(buf, sizeof(buf), "[OK] Fan duty set to %u/255 (LUT disabled)",
                 static_cast<unsigned>(val));
        out.println(buf);
    }
}

static void handleCoolingPump(const char* args, Print& out) {
    if (*args == '\0') {
        out.println(F("[ERR] Usage: cooling pump <0-255> | <0-100%>"));
        out.println(F("       Plain number  = raw duty cycle (0-255)"));
        out.println(F("       With '%'      = pump speed 0-100%% (normalised)"));
        out.println(F("       'cooling on'  = restore LUT control"));
        return;
    }

    // Parse up to 4 digits.
    uint16_t val    = 0;
    uint8_t  digits = 0;
    const char* p = args;
    while (*p >= '0' && *p <= '9' && digits < 4u) {
        val = static_cast<uint16_t>(val * 10u + static_cast<uint16_t>(*p - '0'));
        ++p;
        ++digits;
    }

    if (digits == 0) {
        char buf[96];
        snprintf(buf, sizeof(buf),
                 "[ERR] cooling pump: invalid argument '%s' (expected <duty> or <%%>)", args);
        out.println(buf);
        return;
    }

    // Check for optional trailing '%' to select percent mode.
    const bool isPercent = (*p == '%');
    if (isPercent) { ++p; }

    // Reject trailing non-whitespace garbage.
    if (*p != '\0' && *p != ' ' && *p != '\t') {
        char buf[96];
        snprintf(buf, sizeof(buf),
                 "[ERR] cooling pump: invalid argument '%s' (expected <duty> or <%%>)", args);
        out.println(buf);
        return;
    }

    if (isPercent) {
        // ── Normalised pump speed override (0–100 %) ─────────────────────
        if (val > 100u) {
            out.println(F("[ERR] cooling pump: percentage must be 0-100"));
            return;
        }
        cooling::setPumpSpeed(static_cast<uint8_t>(val));
        char buf[64];
        snprintf(buf, sizeof(buf), "[OK] Pump speed set to %u%% (LUT disabled)",
                 static_cast<unsigned>(val));
        out.println(buf);
    } else {
        // ── Raw duty cycle (0–255) ───────────────────────────────────────
        if (val > 255u) {
            out.println(F("[ERR] cooling pump: duty cycle must be 0-255"));
            return;
        }
        cooling::setPumpDutyCycle(static_cast<uint8_t>(val));
        char buf[48];
        snprintf(buf, sizeof(buf),
                 "[OK] Pump duty set to %u/255 (LUT disabled)",
                 static_cast<unsigned>(val));
        out.println(buf);
    }
}

static void handleFaultPush(const char* args, Print& out) {
    while (*args == ' ' || *args == '\t') ++args;
    if (*args == '\0') {
        out.println(F("[ERR] Usage: fault push <reason>  (numeric mask or name, e.g. RmsOvervoltage)"));
        return;
    }
    if (state_machine::getState() == state_machine::State::Fault) {
        out.println(F("[ERR] Already in fault state — 'fault clear' first"));
        return;
    }
    state_machine::FaultReason reason;
    if (isdigit(static_cast<unsigned char>(*args))) {
        reason = static_cast<state_machine::FaultReason>(strtoul(args, nullptr, 10));
    } else {
        reason = state_machine::parseFaultReason(args);
        if (reason == state_machine::FaultReason::None) {
            out.printf("[ERR] Unknown fault reason: %s\n", args);
            return;
        }
    }
    state_machine::triggerFault(reason);
    char reasonTxtBuf[96];
    state_machine::formatFaultReasons(reason, reasonTxtBuf, sizeof(reasonTxtBuf));
    out.printf("[OK] Fault pushed: %s\n", reasonTxtBuf);
}

static void handleFaultClear(const char* /*args*/, Print& out) {
    if (state_machine::getState() != state_machine::State::Fault) {
        out.println(F("[ERR] Not in fault state"));
        return;
    }

    // Capture the active fault mask before it is erased by clearFault().
    char reasonBuf[96];
    state_machine::formatFaultReasons(state_machine::getFaultReason(), reasonBuf, sizeof(reasonBuf));

    // clearFault() → Idle (resets fault reason, backoffs, running = false).
    state_machine::clearFault();

    // If the operator issued 'stop' while in Fault, honour the deferred stop:
    // stay in Idle without auto-starting.  Otherwise resume from the correct
    // temperature-based state (the normal transient-fault path).
    const bool stopped = state_machine::takeDeferredStop();

    if (stopped) {
        char msg[128];
        snprintf(msg, sizeof(msg),
                 "[OK] Fault cleared (%s) — stopped (deferred stop active)",
                 reasonBuf);
        out.println(msg);
    } else {
#ifdef ARDUINO
        const float tempC = sensor_mock::isActive()
                                ? sensor_mock::get().tempC
                                : cold_head::getLastTempC();
        state_machine::start(tempC);
#else
        state_machine::start();
#endif
        char msg[160];
        snprintf(msg, sizeof(msg),
                 "[OK] Fault cleared (%s) — resumed as %s (%.2f C)",
                 reasonBuf,
                 state_machine::stateName(state_machine::getState()),
#ifdef ARDUINO
                 tempC
#else
                 0.0f
#endif
        );
        out.println(msg);
    }
}

static void handleFaultHistory(const char* /*args*/, Print& out) {
    const uint8_t count = state_machine::getFaultHistoryCount();
    if (count == 0) {
        out.println(F("[OK] Fault history: (empty)"));
        out.println("");
        return;
    }
    char header[72];
    snprintf(header, sizeof(header),
             "[OK] Fault history (%u/%u entries, newest first):",
             static_cast<unsigned>(count),
             static_cast<unsigned>(FAULT_HISTORY_LIMIT));
    out.println(header);

    for (uint8_t i = 0; i < count; ++i) {
        const auto rec = state_machine::getFaultRecord(i);

        char enteredBuf[20];
        if (rec.enteredEpoch > 0) {
            struct tm* tinfo = localtime(&rec.enteredEpoch);
            strftime(enteredBuf, sizeof(enteredBuf), "%m/%d %H:%M:%S", tinfo);
        } else {
            strncpy(enteredBuf, "(pre-sync)", sizeof(enteredBuf));
        }

        // Build pipe-delimited reason string (handles single and multi-bit).
        char reasonBuf[96];
        state_machine::formatFaultReasons(rec.reason, reasonBuf, sizeof(reasonBuf));

        char line[160];
        if (rec.clearedBy == nullptr) {
            snprintf(line, sizeof(line),
                     "  [%2u] %-s  entered: %-14s  ACTIVE",
                     static_cast<unsigned>(i),
                     reasonBuf,
                     enteredBuf);
        } else {
            char clearedBuf[20];
            if (rec.clearedEpoch > 0) {
                struct tm* tinfo = localtime(&rec.clearedEpoch);
                strftime(clearedBuf, sizeof(clearedBuf), "%m/%d %H:%M:%S", tinfo);
            } else {
                strncpy(clearedBuf, "(pre-sync)", sizeof(clearedBuf));
            }
            // Map raw cause strings to human-readable labels.
            const char* clearLabel;
            if (strncmp(rec.clearedBy, "clearFault", 10) == 0) {
                clearLabel = "manual";
            } else if (strncmp(rec.clearedBy, "reinit", 6) == 0) {
                clearLabel = "reinit";
            } else {
                clearLabel = rec.clearedBy;
            }
            snprintf(line, sizeof(line),
                     "  [%2u] %s  entered: %-14s  cleared: %-14s  by: %s",
                     static_cast<unsigned>(i),
                     reasonBuf,
                     enteredBuf,
                     clearedBuf,
                     clearLabel);
        }
        out.println(line);
    }
    out.println("");
}

static void handleBoard(const char* /*args*/, Print& out) {
    out.println(F("[OK] Board info:"));
#ifdef ARDUINO_VARIANT
    out.println("  ARDUINO_VARIANT:        " ARDUINO_VARIANT);
#endif
#ifdef CONFIG_IDF_TARGET
    out.println("  CONFIG_IDF_TARGET:      " CONFIG_IDF_TARGET);
#endif
#ifdef ARDUINO_BOARD
    out.println("  ARDUINO_BOARD:          " ARDUINO_BOARD);
#endif
#ifdef CONFIG_ARDUINO_VARIANT
    out.println("  CONFIG_ARDUINO_VARIANT: " CONFIG_ARDUINO_VARIANT);
#endif
#ifdef CONFIG_ARDUINO_BOARD
    out.println("  CONFIG_ARDUINO_BOARD:   " CONFIG_ARDUINO_BOARD);
#endif
#ifdef ARDUINO_ARCH_ESP32
    out.println(F("  ARDUINO_ARCH_ESP32"));
#endif
#ifdef ESP32S3
    out.println(F("  ESP32S3"));
#elif defined(ESP32)
    out.println(F("  ESP32"));
#endif
#if !defined(ARDUINO_VARIANT) && !defined(CONFIG_IDF_TARGET) && \
    !defined(ARDUINO_BOARD)   && !defined(ESP32)
    out.println(F("  (native / host build — no board macros defined)"));
#endif
}

#ifdef ARDUINO
static void handleI2cScan(const char* /*args*/, Print& out) {
    utils::i2cScan(out);
}
#endif

static void handleFsmState(const char* /*args*/, Print& out) {
    const auto    s         = state_machine::getState();
    const uint32_t inStateMs = state_machine::getTimeInState();
    char buf[128];
    snprintf(buf, sizeof(buf),
             "[OK] %s (%d) | running: %s | in state: %lums\n      %s",
             state_machine::stateName(s),
             static_cast<int8_t>(s),
             state_machine::isRunning() ? "yes" : "no",
             static_cast<unsigned long>(inStateMs),
             state_machine::getStatusText());
    out.println(buf);
    out.println("");
}

static void handleFsmHistory(const char* /*args*/, Print& out) {
    const uint8_t count = state_machine::getHistoryCount();
    if (count == 0) {
        out.println(F("[OK] FSM history: (empty)"));
        out.println("");
        return;
    }
    char header[64];
    snprintf(header, sizeof(header),
             "[OK] FSM history (%u/%u entries, newest first):",
             static_cast<unsigned>(count),
             static_cast<unsigned>(FSM_HISTORY_LIMIT));
    out.println(header);
    for (uint8_t i = 0; i < count; ++i) {
        const auto entry = state_machine::getHistoryEntry(i);

        // Format wall-clock time if SNTP has synced, otherwise flag as pre-sync.
        char timeBuf[20];
        if (entry.enteredEpoch > 0) {
            struct tm* tinfo = localtime(&entry.enteredEpoch);
            strftime(timeBuf, sizeof(timeBuf), "%m/%d %H:%M:%S", tinfo);
        } else {
            strncpy(timeBuf, "(pre-sync)", sizeof(timeBuf));
        }

        char line[112];
        snprintf(line, sizeof(line), "  [%2u] %-16s  %-14s  T+%lu ms  via %s",
                 static_cast<unsigned>(i),
                 state_machine::stateName(entry.state),
                 timeBuf,
                 static_cast<unsigned long>(entry.enteredMs),
                 entry.cause ? entry.cause : "?");
        out.println(line);
    }
    out.println("");
}

static void handleSummary(const char* /*args*/, Print& out) {
    const uint32_t durationMs = state_machine::getOnStateDuration();
    const uint32_t durSec     = durationMs / 1000u;
    char hmsBuf[12];
    snprintf(hmsBuf, sizeof(hmsBuf), "%02lu:%02lu:%02lu",
             static_cast<unsigned long>(durSec / 3600u),
             static_cast<unsigned long>((durSec % 3600u) / 60u),
             static_cast<unsigned long>(durSec % 60u));

    char buf[96];

    out.println(F("[OK] --- Cryocooler Summary ---"));

    snprintf(buf, sizeof(buf), "  State           : %s (%d) | running: %s",
             state_machine::stateName(state_machine::getState()),
             static_cast<int8_t>(state_machine::getState()),
             state_machine::isRunning() ? "yes" : "no");
    out.println(buf);

    snprintf(buf, sizeof(buf), "  On duration     : %s", hmsBuf);
    out.println(buf);

#ifdef ARDUINO
    out.println(F("  --- Cold Head ---"));
    snprintf(buf, sizeof(buf), "  Cold stage      : %.2f C",
             cold_head::getLastTempC());
    out.println(buf);

    // snprintf(buf, sizeof(buf), "  Ambient         : %.2f C",
    //          cold_head::getLastAmbientTempC());
    // out.println(buf);

    snprintf(buf, sizeof(buf), "  Cooling rate    : %.3f C/min",
             cold_head::getCoolingRateCPerMin());
    out.println(buf);

    snprintf(buf, sizeof(buf), "  Cooldown        : %.1f %%",
             cold_head::getTemperatureToPercent());
    out.println(buf);

    out.println(F("  --- Electrical ---"));
    snprintf(buf, sizeof(buf), "  RMS current     : %.3f A",
             amplifier::getLastRmsCurrent());
    out.println(buf);

    snprintf(buf, sizeof(buf), "  RMS voltage     : %.2f V",
             amplifier::getLastRmsVoltage());
    out.println(buf);

    // snprintf(buf, sizeof(buf), "  DAC output      : %u",
    //          static_cast<unsigned>(dac::getCurrent()));
    // out.println(buf);

    out.println(F("  --- Indicators ---"));
    snprintf(buf, sizeof(buf), "  Fault LED       : %s",
             indicator::isFaultOn() ? "ON" : "off");
    out.println(buf);

    snprintf(buf, sizeof(buf), "  Ready LED       : %s",
             indicator::isReadyOn() ? "ON" : "off");
    out.println(buf);
#endif
}

#ifdef ARDUINO

// ─── OTA command handlers ─────────────────────────────────────────────────────

/**
 * Print OTA module status: running partition, next update target, firmware
 * version, OTA endpoint URL, and the last update outcome.
 */
static void handleOtaStatus(const char* /*args*/, Print& out) {
    out.println(F("[OK] OTA status:"));

    // ── Running partition ──────────────────────────────────────────────────
    const esp_partition_t* running = esp_ota_get_running_partition();
    const esp_partition_t* next    = esp_ota_get_next_update_partition(nullptr);
    const esp_app_desc_t*  desc    = esp_ota_get_app_description();

    char buf[96];
    snprintf(buf, sizeof(buf), "  Running partition  : %s",
             running ? running->label : "(unknown)");
    out.println(buf);

    snprintf(buf, sizeof(buf), "  Next update target : %s",
             next ? next->label : "(none — OTA partition missing!)");
    out.println(buf);

    snprintf(buf, sizeof(buf), "  Firmware version   : %s", desc->version);
    out.println(buf);

    snprintf(buf, sizeof(buf), "  Build              : %s %s", desc->date, desc->time);
    out.println(buf);

    // ── Network ───────────────────────────────────────────────────────────
    if (WiFi.status() == WL_CONNECTED) {
        snprintf(buf, sizeof(buf), "  Upload endpoint    : http://%s/ota",
                 WiFi.localIP().toString().c_str());
        out.println(buf);
    } else {
        out.println(F("  Upload endpoint    : (WiFi not connected)"));
    }

    // ── Last update outcome ────────────────────────────────────────────────
    snprintf(buf, sizeof(buf), "  Last OTA result    : %s", ota::getStatusText());
    out.println(buf);

    if (ota::getStatus() == ota::Status::FAILED && ota::getLastError()[0] != '\0') {
        snprintf(buf, sizeof(buf), "  Last error         : %s", ota::getLastError());
        out.println(buf);
    }

    out.println("");
}

/**
 * Arm the OTA confirmation gate.
 *
 * Checks safety conditions (system not running, WiFi up) and, if all clear,
 * sets the s_awaitingUpdateConfirm flag and prompts the operator to type
 * 'yes' to confirm.  The next processLine() call is intercepted:
 *   • "yes"   → print the OTA URL and confirm the endpoint is ready
 *   • anything else → cancel
 */
static void handleUpdateImage(const char* /*args*/, Print& out) {
    // Reject if the cryocooler is running.
    if (state_machine::isRunning()) {
        char buf[96];
        snprintf(buf, sizeof(buf),
                 "[ERR] Cannot update firmware while system is running (%s). "
                 "Stop or off the system first.",
                 state_machine::stateName(state_machine::getState()));
        out.println(buf);
        return;
    }

    // Warn if WiFi is down (user will not be able to reach /ota).
    const bool wifiUp = (WiFi.status() == WL_CONNECTED);

    out.println(F("[CONFIRM] Firmware update requested."));
    out.println(F("  WARNING: Uploading new firmware will REBOOT the device."));
    out.println(F("           The cryocooler will stop immediately on reboot."));
    if (!wifiUp) {
        out.println(F("  WARNING: WiFi is not connected — the /ota endpoint will"));
        out.println(F("           be unreachable until WiFi reconnects."));
    }
    out.println(F("  Type 'yes' to confirm, or anything else to cancel."));
    out.println("");

    s_awaitingUpdateConfirm = true;
}

#endif  // ARDUINO

// ─── Relay command handlers ───────────────────────────────────────────────────
#ifdef ARDUINO

static void handleRelayStatus(const char* /*args*/, Print& out) {
    char buf[48];
    snprintf(buf, sizeof(buf), "[OK] relay.compressor : %s",
             compressor::getStatus() ? "ON" : "off");
    out.println(buf);
    snprintf(buf, sizeof(buf), "     relay.amplifier  : %s",
             amplifier::getRelayState() ? "ON" : "off");
    out.println(buf);
}

static void handleRelayAmplifier(const char* args, Print& out) {
    if (strncmp(args, "on",  2) == 0 && (args[2] == '\0' || args[2] == ' ' || args[2] == '\t')) {
        amplifier::setRelayState(true);
        out.println(F("[OK] relay.amplifier = ON"));
    } else if (strncmp(args, "off", 3) == 0 && (args[3] == '\0' || args[3] == ' ' || args[3] == '\t')) {
        amplifier::setRelayState(false);
        out.println(F("[OK] relay.amplifier = off"));
    } else {
        out.println(F("[ERR] Usage: relay amplifier <on|off>"));
    }
}

static void handleRelayCompressor(const char* args, Print& out) {
    if (strncmp(args, "on",  2) == 0 && (args[2] == '\0' || args[2] == ' ' || args[2] == '\t')) {
        compressor::setRelayState(true);
        out.println(F("[OK] relay.compressor = ON"));
    } else if (strncmp(args, "off", 3) == 0 && (args[3] == '\0' || args[3] == ' ' || args[3] == '\t')) {
        compressor::setRelayState(false);
        out.println(F("[OK] relay.compressor = off"));
    } else {
        out.println(F("[ERR] Usage: relay compressor <on|off>"));
    }
}

#endif  // ARDUINO (relay handlers)

// ─── Compressor command handlers ──────────────────────────────────────────────
#ifdef ARDUINO

static void handleCompressorStart(const char* args, Print& out) {
    if (*args == '\0') {
        out.println(F("[ERR] Usage: compressor start <duration>  e.g.  1h30m0s  |  30m  |  45s"));
        return;
    }
    char errBuf[48];
    const uint32_t durationMs = conversions::parseDurationMs(args, errBuf, sizeof(errBuf));
    if (durationMs == 0u) {
        char buf[96];
        snprintf(buf, sizeof(buf),
                 "[ERR] compressor start: bad duration \"%s\" (%s)", args, errBuf);
        out.println(buf);
        return;
    }

    compressor::startRun(durationMs);

    // Display the actual (possibly clamped) remaining time.
    char hmsBuf[24];
    conversions::formatDurationMs(compressor::getRemainingMs(), hmsBuf, sizeof(hmsBuf));
    char buf[72];
    snprintf(buf, sizeof(buf), "[OK] Compressor started — run time: %s", hmsBuf);
    out.println(buf);
}

static void handleCompressorStatus(const char* /*args*/, Print& out) {
    if (!compressor::getStatus()) {
        out.println(F("[OK] Compressor: OFF (idle)"));
        return;
    }
    out.println(F("[OK] Compressor: ON"));
    if (compressor::isTimedRunActive()) {
        char buf[48];
        char hmsBuf[24];
        conversions::formatDurationMs(compressor::getElapsedMs(), hmsBuf, sizeof(hmsBuf));
        snprintf(buf, sizeof(buf), "  Elapsed  : %s", hmsBuf);
        out.println(buf);
        conversions::formatDurationMs(compressor::getRemainingMs(), hmsBuf, sizeof(hmsBuf));
        snprintf(buf, sizeof(buf), "  Remaining: %s", hmsBuf);
        out.println(buf);
    } else {
        out.println(F("  (no timed run active)"));
    }
    out.println("");
}

static void handleCompressorStop(const char* /*args*/, Print& out) {
    if (!compressor::getStatus()) {
        out.println(F("[ERR] Compressor is not running"));
        return;
    }
    compressor::stopRun();
    out.println(F("[OK] Compressor stopped"));
}

#endif  // ARDUINO (compressor handlers)

// ─── Log level ────────────────────────────────────────────────────────────────

#ifdef ARDUINO
#include <esp_log.h>

static constexpr uint8_t LOG_LEVEL_COUNT = ESP_LOG_VERBOSE + 1;

static constexpr const char* logLevelNames[LOG_LEVEL_COUNT] = {
    "Off", "Error", "Warn", "Info", "Debug", "Verbose"
};

/**
 * Parse a log-level argument string into an esp_log_level_t.
 * Accepts numeric ("0"–"5") or named (case-insensitive: off, error, warn, info, debug, verbose).
 * Returns -1 on invalid input.
 */
static int parseLogLevel(const char* arg) {
    if (arg[0] >= '0' && arg[0] < ('0' + LOG_LEVEL_COUNT) && arg[1] == '\0') {
        return arg[0] - '0';
    }
    for (uint8_t i = 0; i < LOG_LEVEL_COUNT; ++i) {
        if (strcasecmp(arg, logLevelNames[i]) == 0) return i;
    }
    return -1;
}

static void handleLogLevel(const char* args, Print& out) {
    const int level = parseLogLevel(args);

    if (level < 0) {
        out.println(F("[ERR] Usage: log level <0-5|off|error|warn|info|debug|verbose>"));
        return;
    }

    esp_log_level_set("*", static_cast<esp_log_level_t>(level));

    char buf[48];
    snprintf(buf, sizeof(buf), "[OK] Log level set to %s (%d)", logLevelNames[level], level);
    out.println(buf);
}
#endif  // ARDUINO (log level)

static void handleShutdown(const char* /*args*/, Print& out) {
    pinMode(PWR_KILL_PIN, OUTPUT);
    out.println(F("[OK] Shutdown requested... This will require a manual power on to restart"));
    digitalWrite(PWR_KILL_PIN, LOW);
    delay(100);
    digitalWrite(PWR_KILL_PIN, HIGH);
    out.println(F("[OK] System shutdown"));
}

// ─── Command table ────────────────────────────────────────────────────────────
// Multi-word commands ("telemetry off") must appear before any shorter prefix
// command ("telemetry on") so the match loop finds the most specific one first.

static const Command commandMap[] = {
    {"start",         handleStart,        "Begin the cooldown process (from Off or Idle)"},
    {"stop",          handleStop,         "Abort the process and return to Idle"},
    {"off",           handleOff,          "Power off the system entirely"},
    {"reboot",        handleReboot,       "Reboot the system"},
    {"status",        handleStatus,       "Print current state and running flag"},
    {"summary",       handleSummary,      "Print a full snapshot of all system values"},
    // "fsm history" must precede "fsm state" so the longer prefix wins.
    {"fsm history",   handleFsmHistory,   "Print recent FSM state transitions (newest first)"},
    {"fsm state",     handleFsmState,     "Print current FSM state with time-in-state and status"},
    // "fault history" must precede "fault clear" so the longer prefix wins.
    {"fault history", handleFaultHistory, "Print fault log with reason and clear method (newest first)"},
    {"fault push",    handleFaultPush,    "Push a fault record"},
    {"fault clear",   handleFaultClear,   "Clear an active fault and return to Idle"},
    {"board",         handleBoard,        "Print compile-time board/platform info"},
    {"help",          handleHelp,         "Show available commands"},
#ifdef ARDUINO
    {"i2c scan",      handleI2cScan,      "Scan I2C bus and print all responding device addresses"},
#endif
#ifdef ARDUINO
    {"reinit",        handleReinit,       "Re-initialize modules: 'reinit' (all) or 'reinit <name> [name...]'"},
#endif
    // "telemetry delta ..." must precede "telemetry on/off" so the longer
    // prefix is matched first by the linear scan in processLine().
    {"telemetry delta off", handleTelemetryDeltaOff, "Emit full frame each tick (default)"},
    {"telemetry delta on",  handleTelemetryDeltaOn,  "Emit only changed values each tick"},
    {"telemetry off",       handleTelemetryOff,      "Disable telemetry output"},
    {"telemetry on",        handleTelemetryOn,       "Enable telemetry output"},
    // "cooling fan/pump <N>" must precede "cooling on/off" so the longer prefix wins.
    {"cooling fan",         handleCoolingFan,         "Set fan: <0-255> raw duty or <0-100%> percent. 'cooling on' restores LUT."},
    {"cooling pump",        handleCoolingPump,        "Set pump: <0-255> raw duty or <0-100%> percent. 'cooling on' restores LUT."},
    {"cooling on",          handleCoolingOn,           "Enable cooling system"},
    {"cooling off",         handleCoolingOff,          "Disable cooling system"},
#ifdef ARDUINO
    {"dashboard off",       handleDashboardOff, "Disable dashboard TCP broadcasts"},
    {"dashboard on",        handleDashboardOn,  "Enable dashboard TCP broadcasts"},
    // "mock" is a catch-all; subcommands are parsed inside mock_commands::handleMock().
    // Must follow any more-specific "mock ..." entries if those are ever added.
    {"mock",                mock_commands::handleMock, "Sensor mock: enable|disable|status|temp|rate|rms|current|voltage|stall|stroke"},
    {"dac raw",             handleDacRaw,          "Raw SPI write to MCP4921 (0-4095) — bypasses firmware DAC management"},
    {"set vout",            handleVoutSet,         "Set dac output voltage (0-120V, 0-100%, or 'auto' to resume FSM)"},
    {"get vout",            handleVoutGet,         "Get dac output voltage"},
    // "relay amplifier/compressor" must precede bare "relay" so the longer prefix wins.
    {"relay amplifier",     handleRelayAmplifier,   "Energise or de-energise the amplifier relay (on|off)"},
    {"relay compressor",    handleRelayCompressor,  "Energise or de-energise the compressor relay (on|off)"},
    {"relay",               handleRelayStatus,      "Show current state of both relays"},
    // "compressor start" and "compressor status" share the prefix "compressor st";
    // they are distinct because the match requires the full name, so order doesn't
    // matter for correctness, but keep them together for readability.
    {"compressor start",    handleCompressorStart,  "Start compressor run for <duration> (e.g. 1h30m, 45s)"},
    {"compressor status",   handleCompressorStatus, "Show compressor state, elapsed, and remaining run time"},
    {"compressor stop",     handleCompressorStop,   "Stop the compressor immediately"},
    // OTA — "ota status" must precede any future "ota ..." entries.
    {"ota status",          handleOtaStatus,       "Print OTA partition info, firmware version, and endpoint URL"},
    {"update image",        handleUpdateImage,     "Flash new firmware via HTTP upload (prompts for confirmation)"},
    {"log level",           handleLogLevel,        "Set runtime log level: <0-5|off|error|warn|info|debug|verbose>"},
    {"shutdown",            handleShutdown,        "Shutdown the system"},
#endif
};

static const uint8_t commandCount =
    static_cast<uint8_t>(sizeof(commandMap) / sizeof(commandMap[0]));

static void handleHelp(const char* /*args*/, Print& out) {
    out.println(F("[OK] Available commands:"));
    for (uint8_t i = 0; i < commandCount; ++i) {
        char line[80];
        snprintf(line, sizeof(line), "  %-16s  %s",
                 commandMap[i].name, commandMap[i].help);
        out.println(line);
    }
    out.println("");
}

// ─── Public API ───────────────────────────────────────────────────────────────

void processLine(const char* line, Print& out) {
    // Skip leading whitespace.
    while (*line == ' ' || *line == '\t') { ++line; }
    if (*line == '\0') return;
    out.printf("[commands] Received > %s\n", line);

#ifdef ARDUINO
    // ── OTA confirmation intercept ────────────────────────────────────────────
    // When the operator has typed 'update image' we enter a confirmation gate.
    // The very next non-empty input is treated as the confirmation response,
    // bypassing normal command dispatch entirely.
    if (s_awaitingUpdateConfirm) {
        s_awaitingUpdateConfirm = false;  // consume the gate unconditionally

        if (strncmp(line, "yes", 3) == 0 && (line[3] == '\0' || line[3] == ' ')) {
            out.println(F("[OK] Firmware update confirmed."));
            if (WiFi.status() == WL_CONNECTED) {
                char buf[96];
                snprintf(buf, sizeof(buf),
                         "     Navigate to http://%s/ota in your browser to upload a .bin file.",
                         WiFi.localIP().toString().c_str());
                out.println(buf);
                snprintf(buf, sizeof(buf),
                         "     Or use: curl -F 'firmware=@firmware.bin' http://%s/ota",
                         WiFi.localIP().toString().c_str());
                out.println(buf);
            } else {
                out.println(F("     (WiFi not connected — connect first, then run 'ota status' for the URL)"));
            }
            out.println("");
        } else {
            out.println(F("[OK] Update cancelled."));
            out.println("");
        }
        return;
    }
#endif

    // Match command names by prefix: the name must exactly fill the start of
    // the line, followed by end-of-string, space, or tab.  Multi-word names
    // like "telemetry off" win over shorter prefixes because of table order.
    for (uint8_t i = 0; i < commandCount; ++i) {
        const size_t nameLen = strlen(commandMap[i].name);
        if (strncmp(commandMap[i].name, line, nameLen) == 0 &&
            (line[nameLen] == '\0' || line[nameLen] == ' ' || line[nameLen] == '\t')) {
            // Strip leading whitespace from whatever follows the command name.
            const char* args = line + nameLen;
            while (*args == ' ' || *args == '\t') { ++args; }
            commandMap[i].handler(args, out);
            return;
        }
    }

    // Unknown — show just the first token so the message stays tidy.
    const char* end = line;
    while (*end && *end != ' ' && *end != '\t') { ++end; }
    char msg[80];
    snprintf(msg, sizeof(msg),
             "[ERR] Unknown command: '%.*s'  (type 'help')",
             static_cast<int>(end - line), line);
    out.println(msg);
}

void init() {
    lineLen    = 0;
    lineBuf[0] = '\0';
}

void service() {
#ifdef ARDUINO
    while (Serial.available()) {
        const char c = static_cast<char>(Serial.read());
        if (c == '\r' || c == '\n') {
            // Accept \r, \n, and \r\n line endings.
            // For \r\n: \r processes the line; the following \n sees an empty
            // buffer (lineLen == 0) and is a no-op — no double dispatch.
            if (lineLen > 0) {
                lineBuf[lineLen] = '\0';
                processLine(lineBuf, Log);
                lineLen = 0;
            }
        } else if (lineLen < maxLineLen) {
            lineBuf[lineLen++] = c;
            lastCharMs = millis();
        }
        // Characters beyond maxLineLen are silently dropped until next newline.
    }

    // Timeout-based dispatch: if bytes accumulated but no line terminator
    // arrived within commandTimeoutMs, treat the buffer as a complete command.
    // Handles monitors / tools (e.g. PlatformIO IDE with "None" EOL) that send
    // the full string as one USB-CDC packet without appending \r or \n.
    if (lineLen > 0 && (millis() - lastCharMs) >= commandTimeoutMs) {
        lineBuf[lineLen] = '\0';
        processLine(lineBuf, Log);
        lineLen = 0;
    }
#endif
}

} // namespace commands
