jhyland87/Cryocooler-Controller/include/conversions.h

/**
 * @file conversions.h
 * @brief Pure math / conversion utilities (no hardware dependencies)
 *
 * These functions are free of Arduino or peripheral includes so they
 * can be compiled and unit-tested natively on the host PC.
 */

#ifndef CONVERSIONS_H
#define CONVERSIONS_H

#include <Arduino.h>
#include <stdint.h>
#include <cmath>


namespace conversions {

/**
 * Convert PT1000 resistance to temperature using Callendar-Van Dusen equation.
 *
 * Above 0 °C: R(T) = R0 * (1 + A*T + B*T^2)  → solve quadratic for T.
 * Below 0 °C: polynomial approximation (Analog Devices AN709).
 *
 * @param R  Measured PT1000 resistance in ohms
 * @return   Temperature in Celsius (NAN if discriminant < 0)
 */
inline float resistanceToTemperaturePT1000(float R) {
    constexpr float R0  = 1000.0f;   // PT1000 nominal at 0 °C
    constexpr float A   = 3.9083e-3f;
    constexpr float B   = -5.775e-7f;

    if (R >= R0) {
        // Above 0 °C: quadratic  B*T^2 + A*T + (1 - R/R0) = 0
        const float disc = (A * A) - 4.0f * B * (1.0f - R / R0);
        if (disc < 0.0f) return NAN;
        return (-A + sqrtf(disc)) / (2.0f * B);
    } else {
        // Below 0 °C: polynomial approximation (AN709, calibrated for PT100).
        // PT1000 resistance is 10× PT100, so normalise before applying.
        const float Rn = R / 10.0f;
        float ret = -242.02f;
        ret += 2.2228f     * Rn;
        float poly = Rn * Rn;
        ret += 2.5859e-3f  * poly;
        poly *= Rn;
        ret -= 4.8260e-6f  * poly;
        poly *= Rn;
        ret -= 2.8183e-8f  * poly;
        poly *= Rn;
        ret += 1.5243e-10f * poly;
        return ret;
    }
}

/**
 * Convert Celsius to Fahrenheit.
 */
inline float celsiusToFahrenheit(float tempC) {
    return tempC * 9.0f / 5.0f + 32.0f;
}

/**
 * Convert Kelvin to Celsius.
 */
inline float kelvinToCelsius(float tempK) {
    return tempK - 273.15f;
}

/**
 * Convert Fahrenheit to Celsius.
 */
inline float fahrenheitToCelsius(float tempF) {
    return (tempF - 32.0f) * 5.0f / 9.0f;
}

/**
 * Map a temperature in Celsius to a 12-bit DAC output value.
 *
 * The DAC output is 0 when the temperature is at or above @p ambientC
 * (the warm / start-of-cooldown reference) and rises linearly to @p maxDac
 * when the temperature reaches @p setpointC.  Values are clamped to [0, maxDac].
 *
 * This function is pure math with no Arduino or hardware dependencies, making
 * it safe to call from native unit tests.
 *
 * @param tempC      Current temperature in Celsius
 * @param ambientC   Reference "warm" temperature (DAC = 0 here)
 * @param setpointC  Target cold temperature (DAC = maxDac here)
 * @param maxDac     Maximum DAC output value (e.g. 4095 for 12-bit)
 * @return           Proportional DAC value clamped to [0, maxDac]
 */
inline uint16_t tempCToDacValue(float tempC,
                                float ambientC,
                                float setpointC,
                                uint16_t maxDac)
{
    if (tempC >= ambientC)   return 0;
    if (tempC <= setpointC)  return maxDac;

    const float span     = ambientC - setpointC;
    const float dropped  = ambientC - tempC;
    const float fraction = dropped / span;

    // Cast via int32 to avoid undefined behaviour on negative fraction edge
    auto raw = static_cast<int32_t>(fraction * static_cast<float>(maxDac));
    if (raw < 0)                         return 0;
    if (raw > static_cast<int32_t>(maxDac)) return maxDac;
    return static_cast<uint16_t>(raw);
}

/**
 * Map a cold-head temperature to a cooldown fraction in [0.0, 1.0].
 *
 * Returns 0.0 when the temperature is at or above @p ambientC and 1.0
 * when it has reached @p setpointC.  Callers multiply by whatever
 * ceiling they need (voltage, DAC counts, etc.).
 *
 * @param tempC      Current cold-head temperature in Celsius
 * @param ambientC   Reference "warm" temperature (fraction = 0 here)
 * @param setpointC  Target cold temperature (fraction = 1 here)
 * @return           Cooldown fraction clamped to [0.0, 1.0]
 */
inline float tempCToFraction(float tempC,
                             float ambientC,
                             float setpointC)
{
    if (tempC >= ambientC)  return 0.0f;
    if (tempC <= setpointC) return 1.0f;

    const float span     = ambientC - setpointC;
    const float dropped  = ambientC - tempC;
    const float fraction = dropped / span;

    if (fraction < 0.0f) return 0.0f;
    if (fraction > 1.0f) return 1.0f;
    return fraction;
}

inline void msToHHMMSS(uint32_t durationMs, char* hmsBuf, size_t len)
{
    const uint32_t totalSec = durationMs / 1000u;
    const uint32_t hh       = totalSec / 3600u;
    const uint32_t mm       = (totalSec % 3600u) / 60u;
    const uint32_t ss       = totalSec % 60u;

    snprintf(hmsBuf, len, "%02lu:%02lu:%02lu",
            static_cast<unsigned long>(hh),
            static_cast<unsigned long>(mm),
            static_cast<unsigned long>(ss));
}

/**
 * Parse a human-readable duration string into milliseconds.
 *
 * Accepts any combination of h/m/s components with optional whitespace
 * between tokens.  All components are optional but at least one must be
 * present.  Unit suffixes are case-insensitive.  Examples:
 *   "1h30m0s"  "30m"  "45s"  "2h"  "1h 30m"  "0h0m30s"
 *
 * @param str     Null-terminated input string.
 * @param errOut  Receives a short error description on failure.
 * @param errLen  Size of errOut in bytes.
 * @return        Total milliseconds, or 0 on parse failure (errOut is set).
 */
inline uint32_t parseDurationMs(const char* str, char* errOut, size_t errLen) {
    uint32_t    totalMs = 0u;
    bool        found   = false;
    const char* p       = str;

    while (*p != '\0') {
        while (*p == ' ' || *p == '\t') { ++p; }
        if (*p == '\0') break;

        if (*p < '0' || *p > '9') {
            snprintf(errOut, errLen, "unexpected character '%c'", *p);
            return 0u;
        }
        uint32_t val = 0u;
        while (*p >= '0' && *p <= '9') {
            val = val * 10u + static_cast<uint32_t>(*p - '0');
            ++p;
        }

        const char unit = *p;
        if (unit == 'h' || unit == 'H') {
            totalMs += val * 3600000u;
        } else if (unit == 'm' || unit == 'M') {
            totalMs += val * 60000u;
        } else if (unit == 's' || unit == 'S') {
            totalMs += val * 1000u;
        } else {
            snprintf(errOut, errLen,
                     "unknown unit '%c' — use h, m, or s", unit ? unit : '?');
            return 0u;
        }
        found = true;
        ++p;
    }

    if (!found) {
        snprintf(errOut, errLen, "no duration components found");
        return 0u;
    }
    return totalMs;
}

/**
 * Format a millisecond count as a compact human-readable duration string.
 *
 * Produces "Xh Ym Zs" when hours > 0, or "Ym Zs" for shorter durations,
 * keeping output tidy for display in serial/TCP command responses.
 *
 * @param ms   Duration in milliseconds.
 * @param buf  Output buffer.
 * @param len  Size of buf in bytes.
 */
inline void formatDurationMs(uint32_t ms, char* buf, size_t len) {
    const uint32_t totalSec = ms / 1000u;
    const uint32_t h        = totalSec / 3600u;
    const uint32_t m        = (totalSec % 3600u) / 60u;
    const uint32_t s        = totalSec % 60u;
    if (h > 0u) {
        snprintf(buf, len, "%luh %02lum %02lus",
                 static_cast<unsigned long>(h),
                 static_cast<unsigned long>(m),
                 static_cast<unsigned long>(s));
    } else {
        snprintf(buf, len, "%lum %02lus",
                 static_cast<unsigned long>(m),
                 static_cast<unsigned long>(s));
    }
}

} // namespace conversions

#endif // CONVERSIONS_H
