jhyland87/Cryocooler-Controller/src/frame_builder.cpp

/**
 * @file frame_builder.cpp
 * @brief FrameBuilder output method implementations.
 */

#ifdef ARDUINO
#  include <Arduino.h>
#else
#  include "Arduino.h"   // native stub — provides Print
#endif

#include <ArduinoJson.h>
#include <cstring>
#include "frame_builder.h"

// ---------------------------------------------------------------------------
// Serial Studio wire format:  /*v1|v2|...|vN*/\r\n
//
// The entire frame is assembled into a single stack buffer before calling
// out.write() once.  This is important on ESP32: the Arduino HWCDC Serial
// implementation flushes its internal ring buffer asynchronously, so making
// ~50 individual print() calls lets the FreeRTOS scheduler preempt between
// them and interleave output from other tasks (WiFi, TCP/IP stack, etc.).
// A single write() keeps the complete frame contiguous in the USB FIFO.
// ---------------------------------------------------------------------------

void FrameBuilder::sendSerial(Print& out) const {
    // Worst-case frame size:
    //   2  ("/*") + MAX_FIELDS * (VALUE_BUF_SIZE + 1) ("val|") + 4 ("*/\r\n") + 1 (NUL)
    constexpr size_t BUF_SIZE =
        2u + static_cast<size_t>(MAX_FIELDS) * (VALUE_BUF_SIZE + 1u) + 4u + 1u;

    char   buf[BUF_SIZE];
    size_t pos = 0u;

    auto append = [&](const char* s, size_t n) {
        if (pos + n >= BUF_SIZE) { return; }   // truncate rather than overflow
        memcpy(buf + pos, s, n);
        pos += n;
    };

    //append("/*", 2u);
    for (uint8_t i = 0u; i < count_; ++i) {
        if (i > 0u) { append("\t", 1u); }
        append(fields_[i].str, strlen(fields_[i].str));
    }
    append("\r\n", 2u);


    out.write(reinterpret_cast<const uint8_t*>(buf), pos);
}

// ---------------------------------------------------------------------------
// Delta serial output — only changed fields, "name=value  name=value\r\n"
//
// A static BSS buffer is used (rather than a stack allocation) because the
// worst-case size — MAX_FIELDS × (field-name + "=" + VALUE_BUF_SIZE + "  ")
// plus "\r\n\0" — exceeds what is safe to allocate on the ESP32 task stack.
// emit() is called from a single FreeRTOS task so there is no reentrancy risk.
// ---------------------------------------------------------------------------
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
